Kevin16437/wheel_legged_robot/solidworks/轮腿装配图/守护兽轮腿.SLDASM

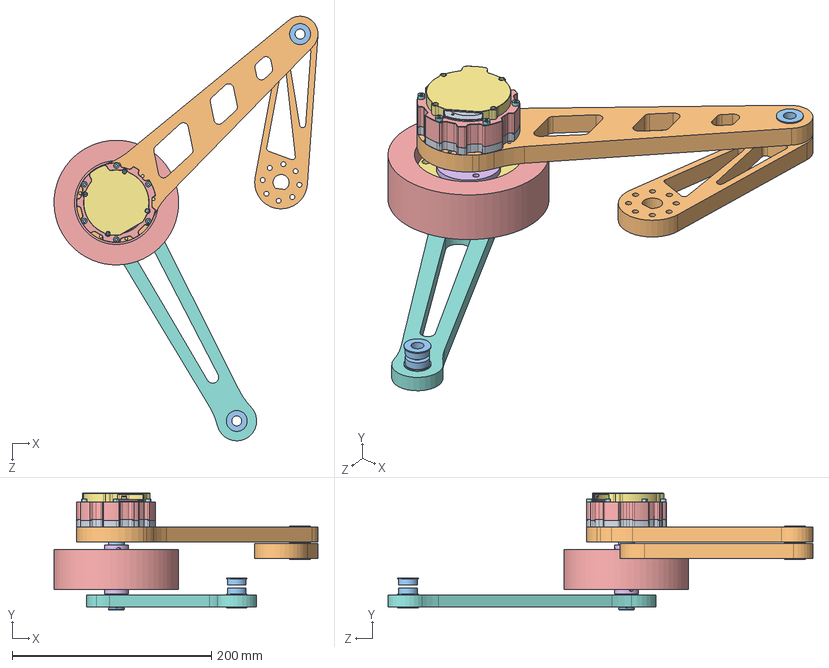
[picture p17: CAD file, 2024-12-23]
solidworks/轮腿装配图/守护兽轮腿.SLDASM
264.7 x 117.1 x 425.9 mm
NONE_1_1^_X2_897F683C00B79A6C51CF901F753_ASM_SG6010D_asm20240708.stp.STEP
SG6010H_ASM_______2__SG6-206444^_X2_897F683C00B79A6C51CF901F753_ASM_SG6010D_asm20240708.stp.STEP
MANIFOLD_SOLID_BREP_439152_1^SG6010C-04_5_ASM_1_ASM_SG6010C_ASM_252_ASM_1_ASM_SG6010D_asm20240708.stp.STEP
MANIFOLD_SOLID_BREP_439299_1^SG6010C-04_5_ASM_1_ASM_SG6010C_ASM_252_ASM_1_ASM_SG6010D_asm20240708.stp.STEP
SG6010C-01_63_1^SG6010C_ASM_252_ASM_1_ASM_SG6010D_asm20240708.stp.STEP
SG6010C-21_6_1^SG6010C_ASM_252_ASM_1_ASM_SG6010D_asm20240708.stp.STEP
SG6010C-02_27_1^SG6010C_ASM_252_ASM_1_ASM_SG6010D_asm20240708.stp.STEP
M3X22_2_1^SG6010C_ASM_252_ASM_1_ASM_SG6010D_asm20240708.stp.STEP x 6
M2X5_2_1^SG6010C_ASM_252_ASM_1_ASM_SG6010D_asm20240708.stp.STEP x 4
小腿臂
传动轴
内30外47高9轴承
轮
法兰内16外22 x 2
轮子固定板 x 2
小腿臂外侧
内16外40高12轴承
大腿臂
内10外19厚7法兰21厚1 x 6
内10外18推力球 x 2
传动轴垫片
4mm轴间垫片
1mm轴间垫片
