Kevin16437/wheel_legged_robot/solidworks/轮腿装配图/西格·马总装模型2024(二级减速).SLDASM

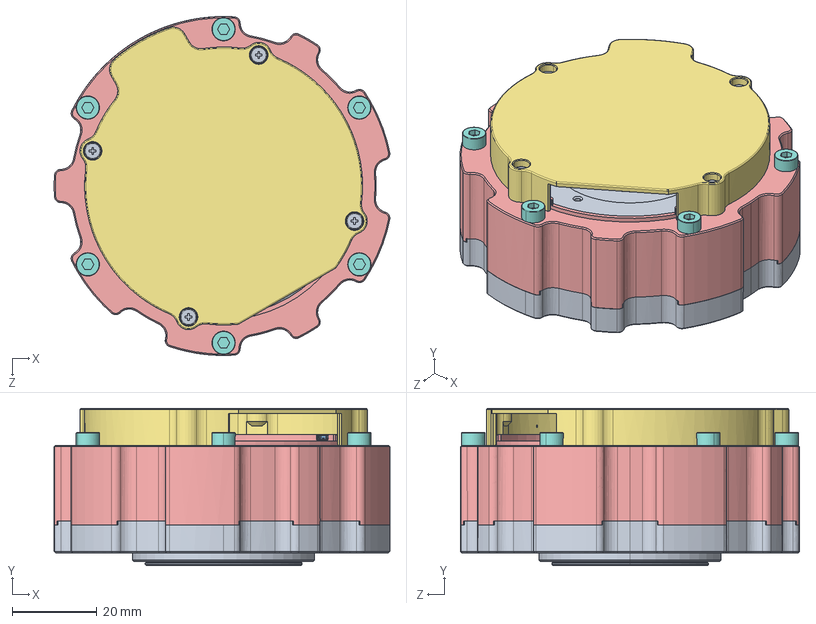
[picture p18: CAD file, 2024-12-23]
solidworks/轮腿装配图/西格·马总装模型2024(二级减速).SLDASM
79.2 x 37.1 x 80.0 mm
NONE_1_1^_X2_897F683C00B79A6C51CF901F753_ASM_SG6010D_asm20240708.stp.STEP
SG6010H_ASM_______2__SG6-206444^_X2_897F683C00B79A6C51CF901F753_ASM_SG6010D_asm20240708.stp.STEP
MANIFOLD_SOLID_BREP_439152_1^SG6010C-04_5_ASM_1_ASM_SG6010C_ASM_252_ASM_1_ASM_SG6010D_asm20240708.stp.STEP
MANIFOLD_SOLID_BREP_439299_1^SG6010C-04_5_ASM_1_ASM_SG6010C_ASM_252_ASM_1_ASM_SG6010D_asm20240708.stp.STEP
SG6010C-01_63_1^SG6010C_ASM_252_ASM_1_ASM_SG6010D_asm20240708.stp.STEP
SG6010C-21_6_1^SG6010C_ASM_252_ASM_1_ASM_SG6010D_asm20240708.stp.STEP
SG6010C-02_27_1^SG6010C_ASM_252_ASM_1_ASM_SG6010D_asm20240708.stp.STEP
M3X22_2_1^SG6010C_ASM_252_ASM_1_ASM_SG6010D_asm20240708.stp.STEP x 6
M2X5_2_1^SG6010C_ASM_252_ASM_1_ASM_SG6010D_asm20240708.stp.STEP x 4
