Kevin16437/wheel_legged_robot/solidworks/轮腿零件step/轮子固定板x4.STEP

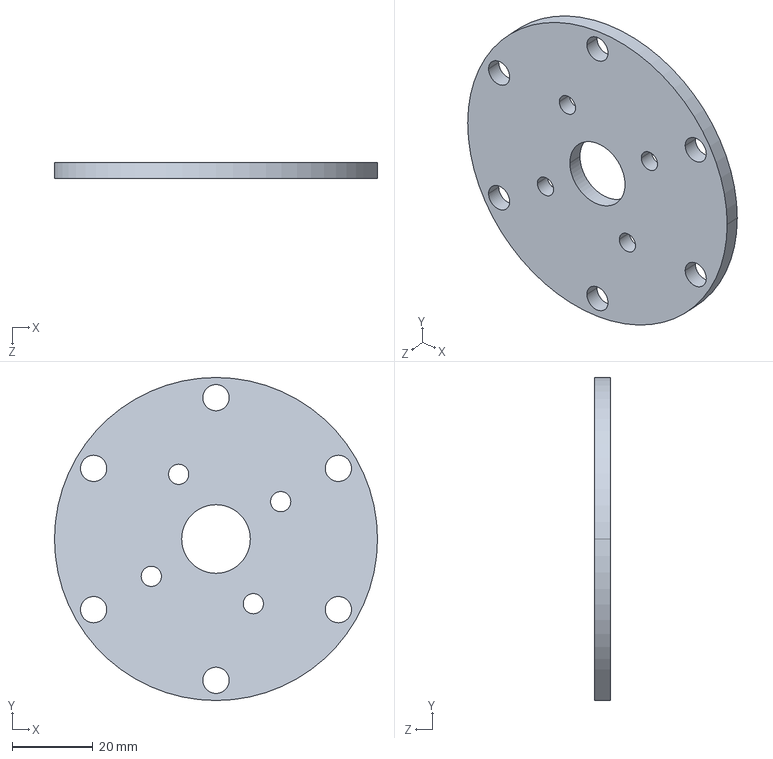
[picture p20: CAD file, 2024-12-23]
solidworks/轮腿零件step/轮子固定板x4.STEP
80.0 x 80.0 x 4.00 mm
