Kevin16437/wheel_legged_robot/solidworks/轮腿零件step/底部电池斜壳x1-碳板.STEP

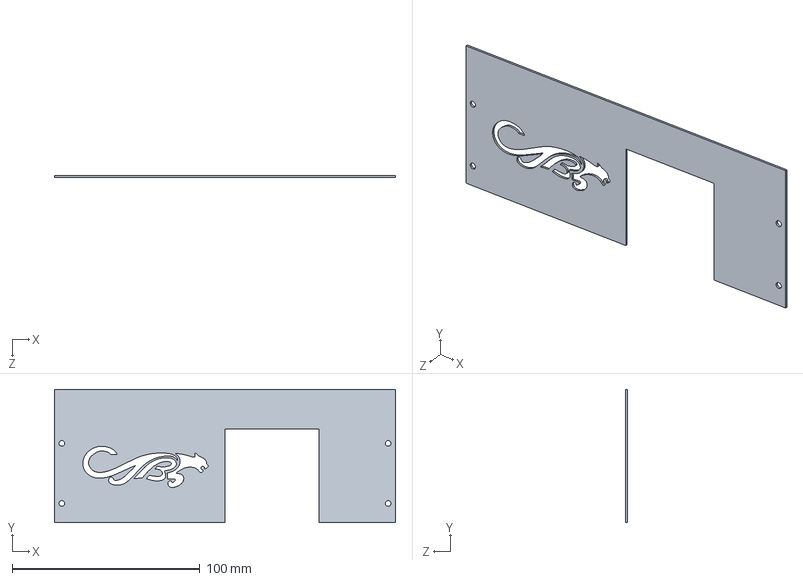
[picture p21: CAD file, 2024-12-23]
solidworks/轮腿零件step/底部电池斜壳x1-碳板.STEP
181.7 x 71.0 x 1.00 mm
