Kevin16437/wheel_legged_robot/solidworks/轮腿零件step/守护兽强挡板x1-碳板.STEP

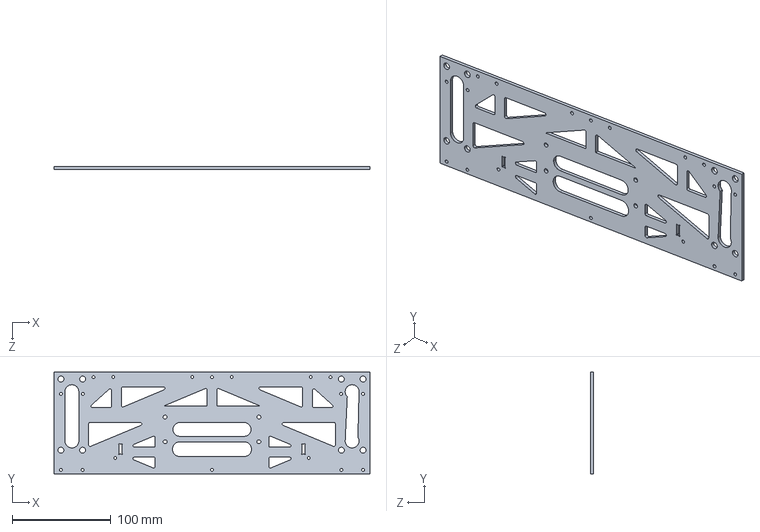
[picture p22: CAD file, 2024-12-23]
solidworks/轮腿零件step/守护兽强挡板x1-碳板.STEP
320.0 x 103.0 x 3.00 mm
