Kevin16437/wheel_legged_robot/solidworks/轮腿零件step/关节电机固定盒x1-碳板.STEP

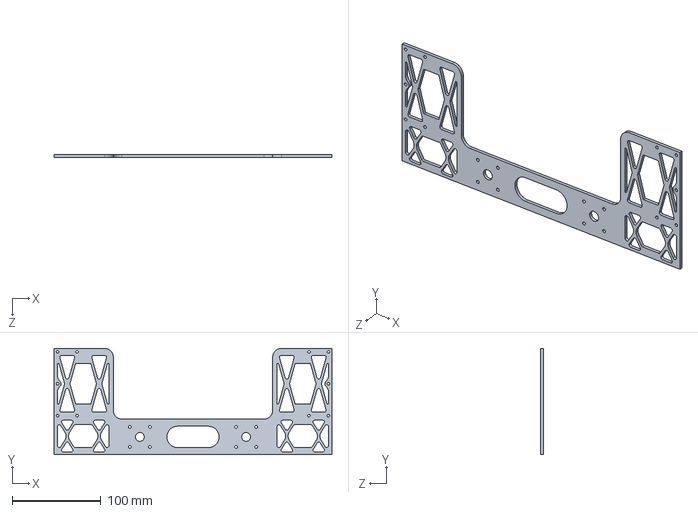
[picture p23: CAD file, 2024-12-23]
solidworks/轮腿零件step/关节电机固定盒x1-碳板.STEP
314.0 x 120.0 x 3.00 mm
