Kevin16437/wheel_legged_robot/solidworks/轮腿零件step/KJ90FT33装配体x2.STEP

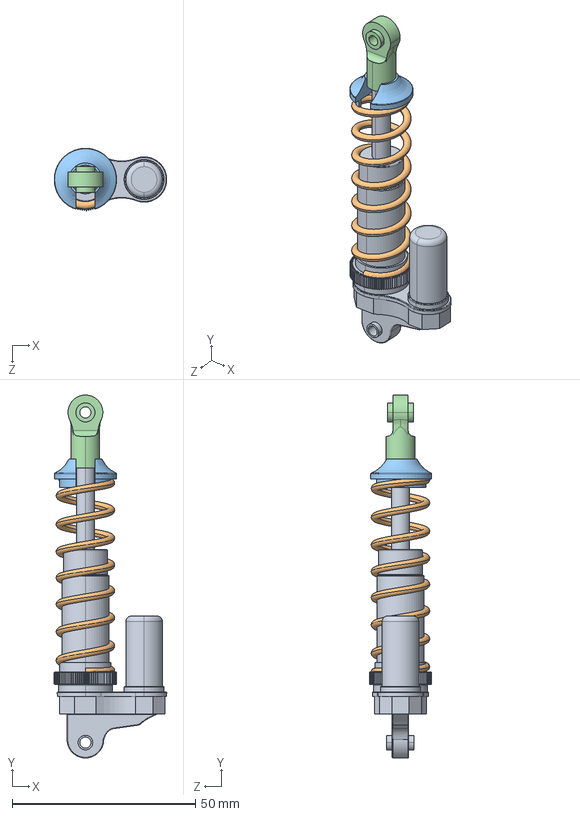
[picture p24: CAD file, 2024-12-23]
solidworks/轮腿零件step/KJ90FT33装配体x2.STEP
30.7 x 99.0 x 17.0 mm
________.STEP
____90____.STEP
________-0.STEP
________-1.STEP
