Kevin16437/wheel_legged_robot/solidworks/轮腿零件step/内10外30厚11导轮x4.STEP

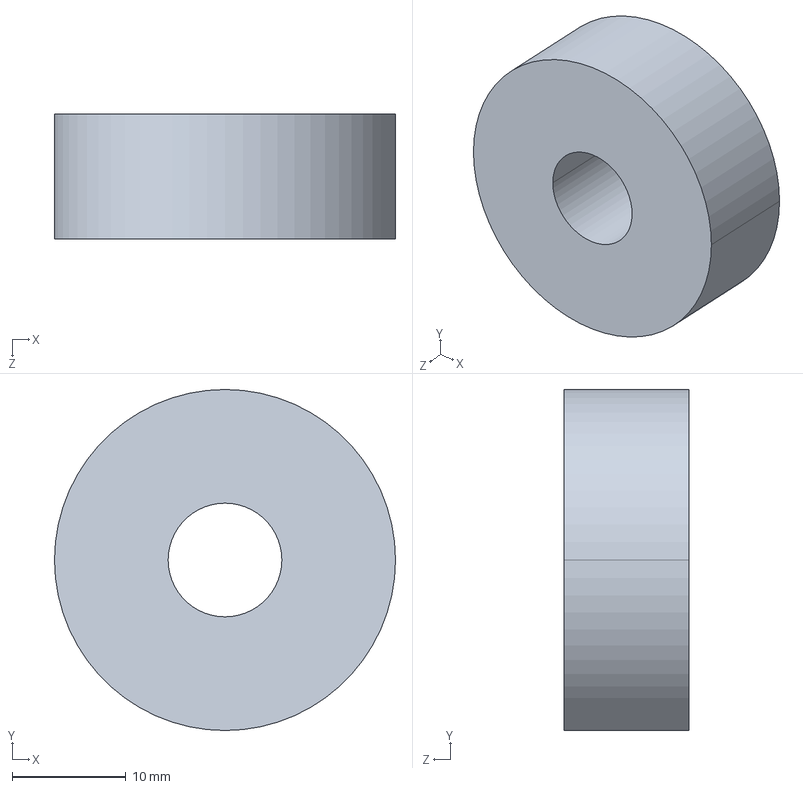
[picture p25: CAD file, 2024-12-23]
solidworks/轮腿零件step/内10外30厚11导轮x4.STEP
30.0 x 30.0 x 11.0 mm
