Kevin16437/wheel_legged_robot/solidworks/轮腿零件step/守护兽强挡板短x1-碳板.STEP

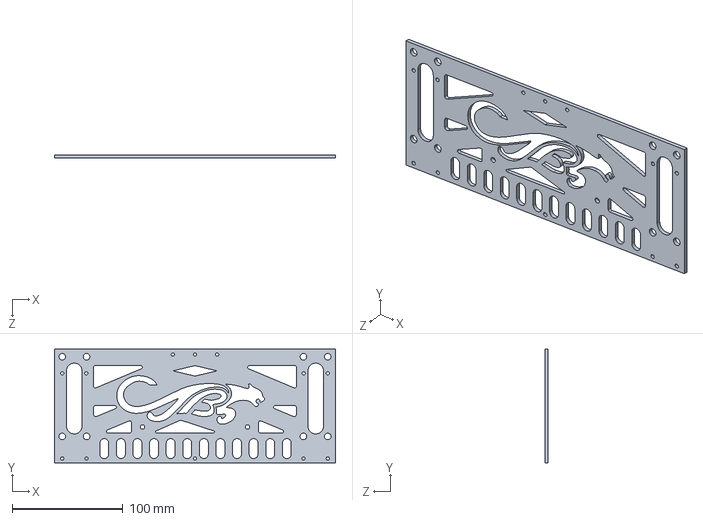
[picture p27: CAD file, 2024-12-23]
solidworks/轮腿零件step/守护兽强挡板短x1-碳板.STEP
254.0 x 103.0 x 3.00 mm
