Kevin16437/wheel_legged_robot/solidworks/轮腿零件step/内16外40高12轴承x4.STEP

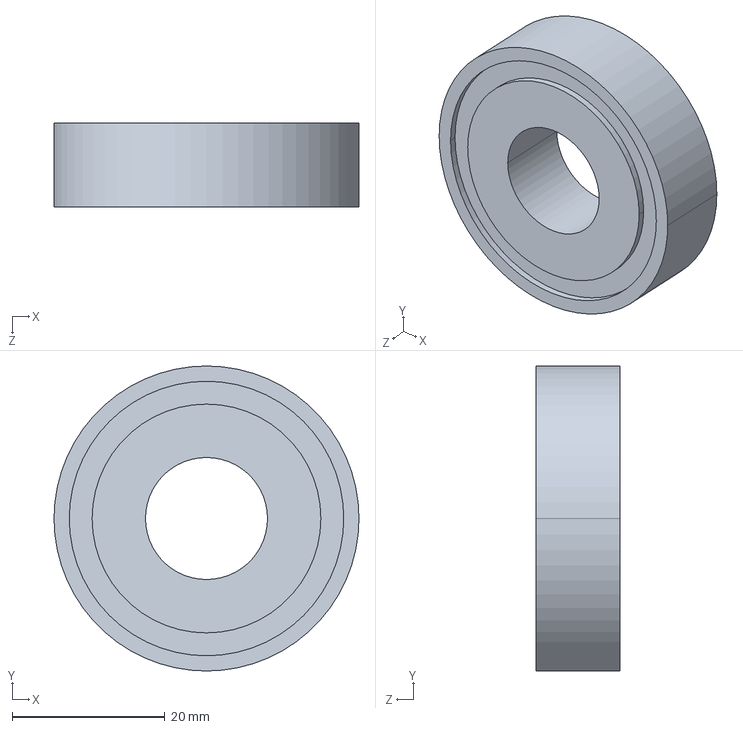
[picture p28: CAD file, 2024-12-23]
solidworks/轮腿零件step/内16外40高12轴承x4.STEP
40.0 x 40.0 x 11.0 mm
