Kevin16437/wheel_legged_robot/solidworks/轮腿零件step/云台底板方避震x1.STEP

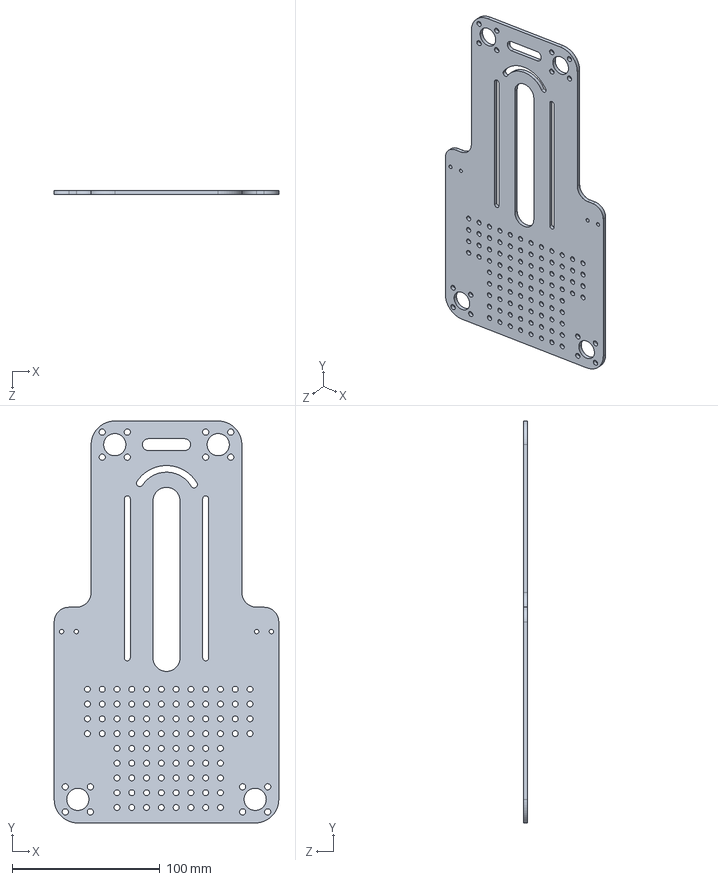
[picture p29: CAD file, 2024-12-23]
solidworks/轮腿零件step/云台底板方避震x1.STEP
152.0 x 272.0 x 3.00 mm
