Kevin16437/wheel_legged_robot/solidworks/轮腿零件step/关节电机固定盒上下x2-碳板.STEP

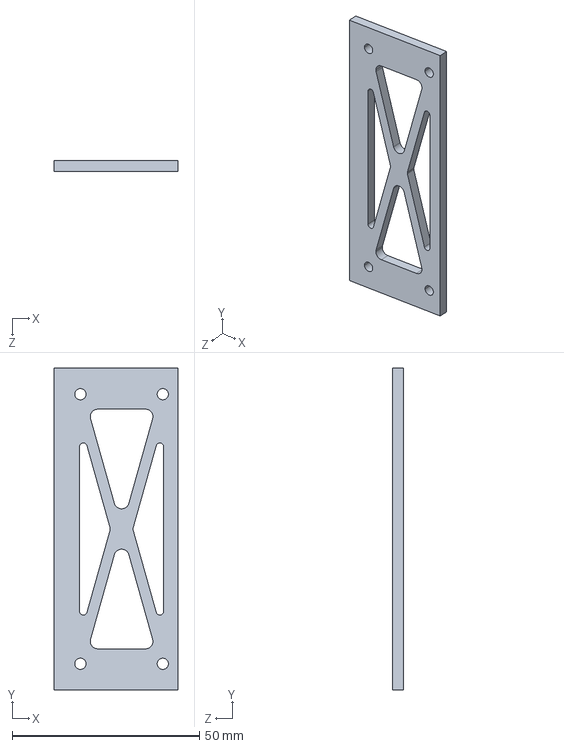
[picture p30: CAD file, 2024-12-23]
solidworks/轮腿零件step/关节电机固定盒上下x2-碳板.STEP
33.0 x 86.0 x 3.00 mm
