Kevin16437/wheel_legged_robot/solidworks/轮腿零件step/电源.STEP

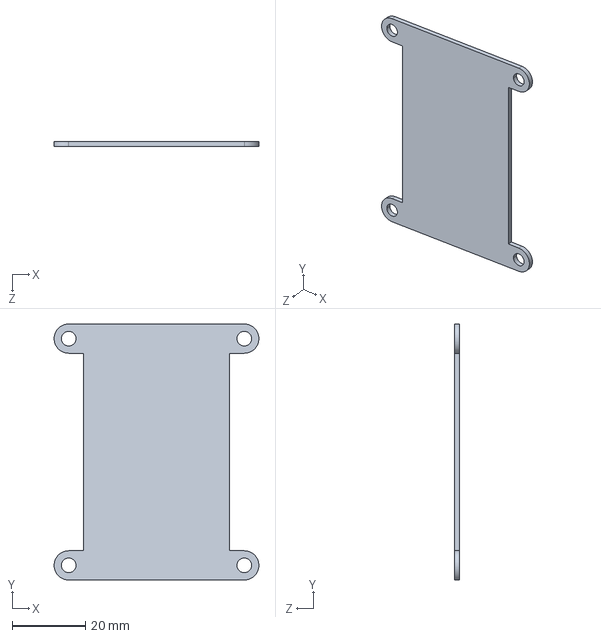
[picture p31: CAD file, 2024-12-23]
solidworks/轮腿零件step/电源.STEP
56.0 x 70.0 x 1.50 mm
