Kevin16437/wheel_legged_robot/solidworks/轮腿零件step/塞打螺栓D10XM8-16x4.STEP

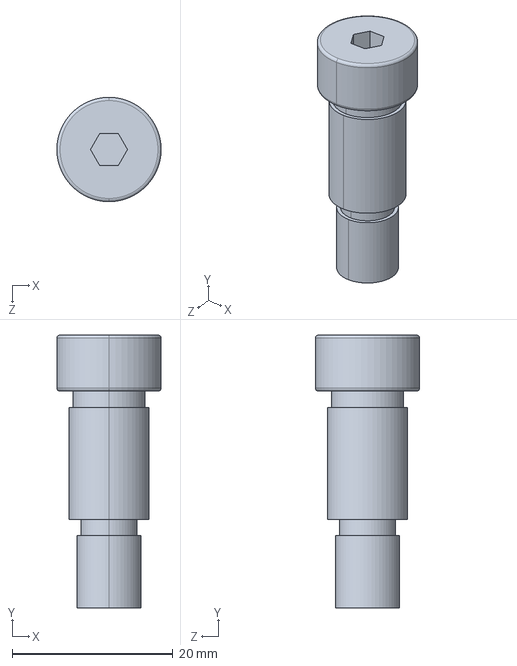
[picture p32: CAD file, 2024-12-23]
solidworks/轮腿零件step/塞打螺栓D10XM8-16x4.STEP
13.0 x 34.0 x 13.0 mm
