Kevin16437/wheel_legged_robot/solidworks/轮腿零件step/四方体固定x44.STEP

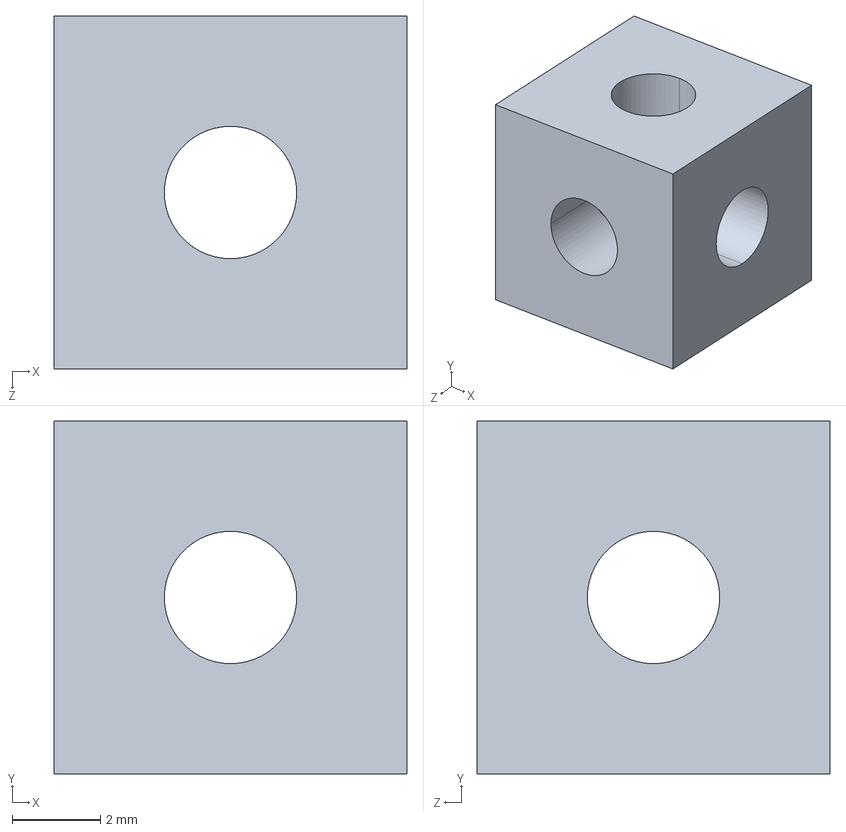
[picture p33: CAD file, 2024-12-23]
solidworks/轮腿零件step/四方体固定x44.STEP
8.00 x 8.00 x 8.00 mm
