Kevin16437/wheel_legged_robot/solidworks/轮腿零件step/限位挡块x2.STEP

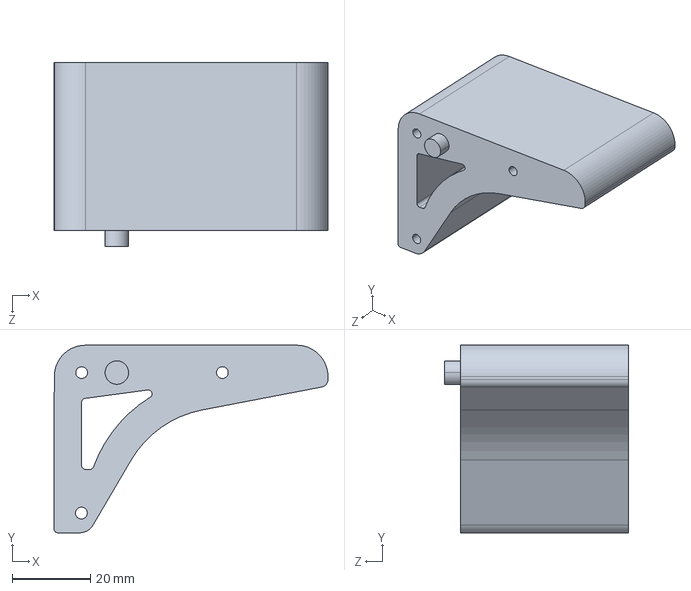
[picture p34: CAD file, 2024-12-23]
solidworks/轮腿零件step/限位挡块x2.STEP
70.1 x 48.0 x 47.0 mm
