Kevin16437/wheel_legged_robot/solidworks/轮腿零件step/轴承挡板x4-碳板.STEP

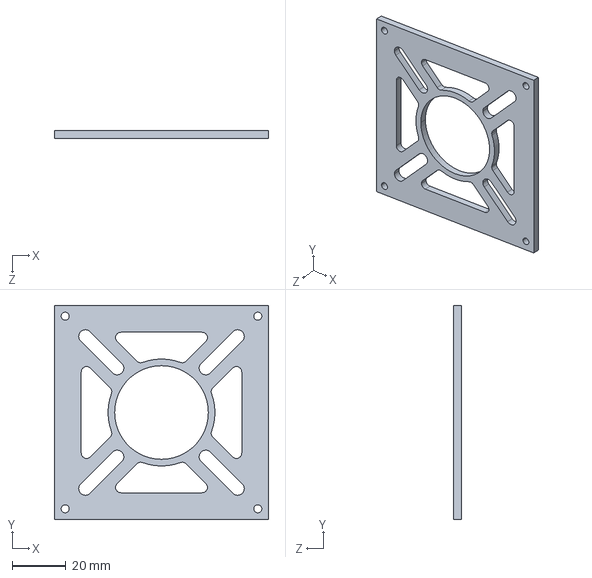
[picture p35: CAD file, 2024-12-23]
solidworks/轮腿零件step/轴承挡板x4-碳板.STEP
80.0 x 80.0 x 3.00 mm
