Kevin16437/wheel_legged_robot/solidworks/轮腿零件step/轴承支撑板整体x2-碳板.STEP

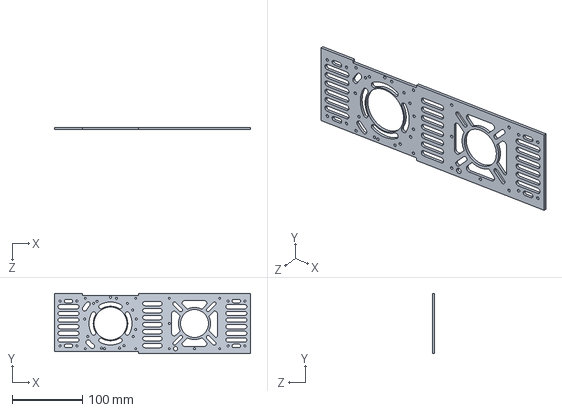
[picture p37: CAD file, 2024-12-23]
solidworks/轮腿零件step/轴承支撑板整体x2-碳板.STEP
280.0 x 86.0 x 3.00 mm
