Kevin16437/wheel_legged_robot/solidworks/轮腿零件step/下底盘保护x2-碳板.STEP

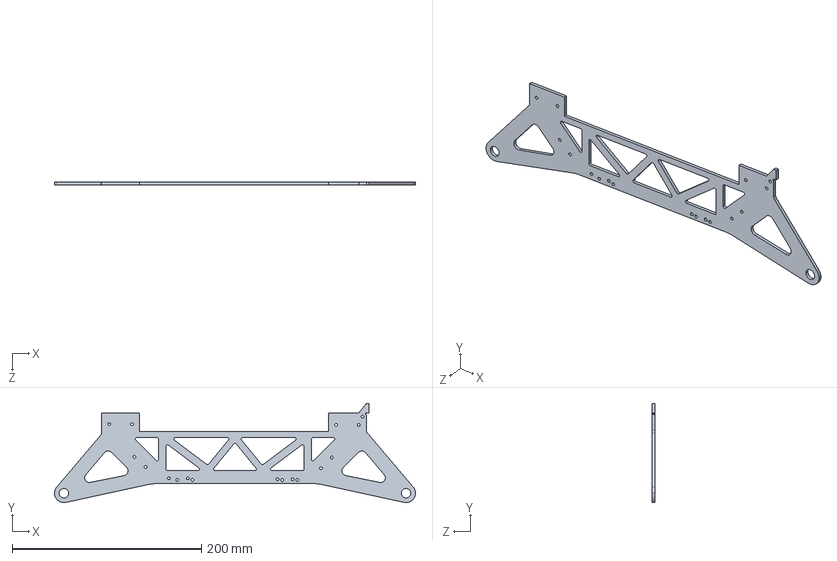
[picture p39: CAD file, 2024-12-23]
solidworks/轮腿零件step/下底盘保护x2-碳板.STEP
382.0 x 105.0 x 3.00 mm
