Kevin16437/wheel_legged_robot/solidworks/轮腿装配图/传动轴.SLDPRT

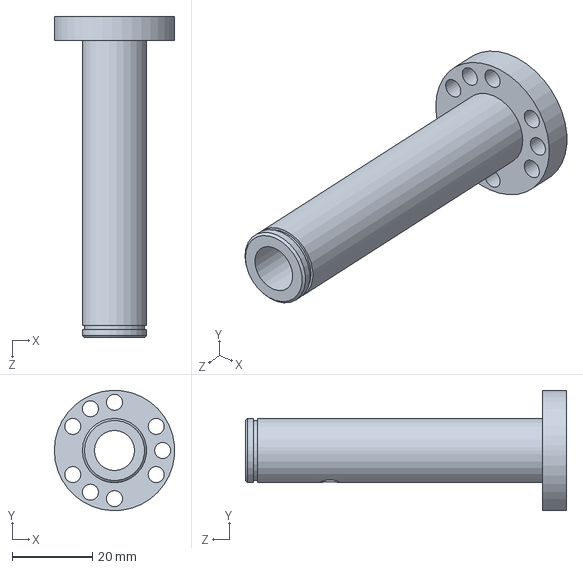
[picture p40: CAD file, 2024-12-23]
solidworks/轮腿装配图/传动轴.SLDPRT
30.0 x 30.0 x 80.0 mm
