Kevin16437/wheel_legged_robot/solidworks/轮腿零件step/长方体固定x8.STEP

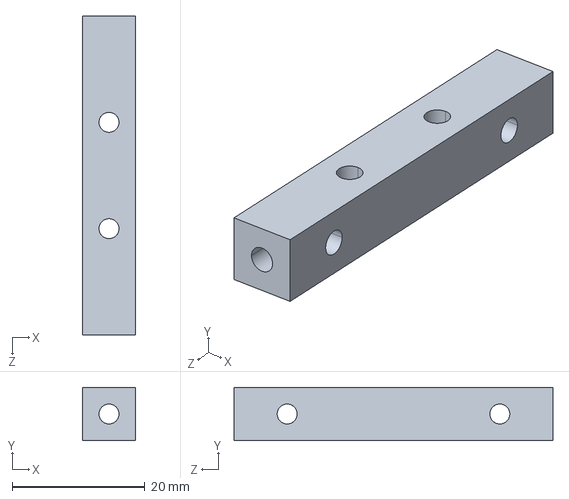
[picture p41: CAD file, 2024-12-23]
solidworks/轮腿零件step/长方体固定x8.STEP
8.00 x 8.00 x 48.0 mm
