Kevin16437/wheel_legged_robot/solidworks/轮腿装配图/大腿臂.SLDPRT

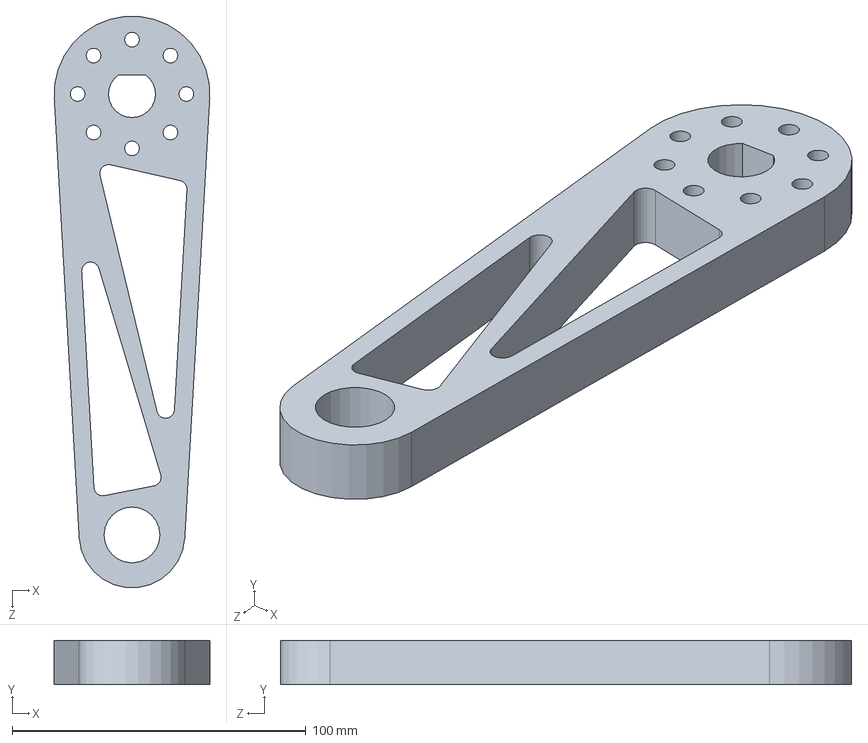
[picture p42: CAD file, 2024-12-23]
solidworks/轮腿装配图/大腿臂.SLDPRT
52.9 x 15.0 x 194.3 mm
