Kevin16437/wheel_legged_robot/solidworks/轮腿零件step/3mm避震安装座x2.STEP

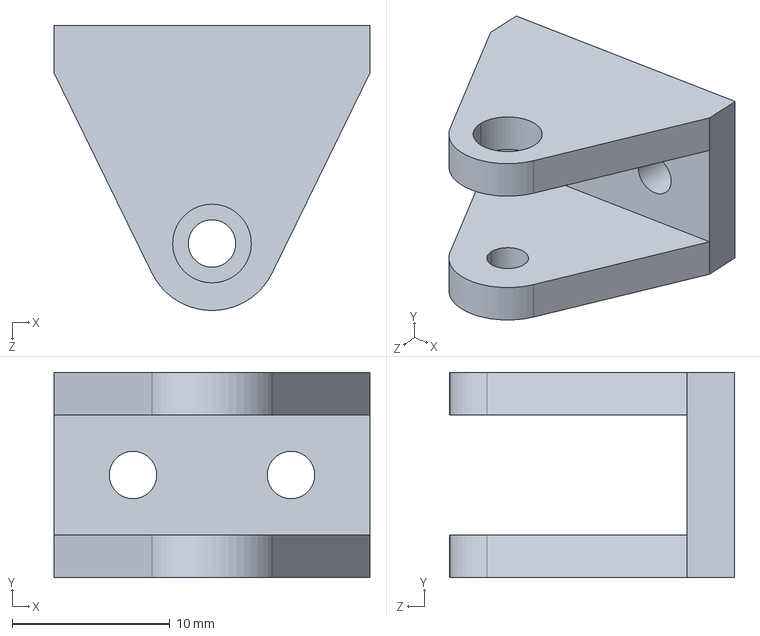
[picture p43: CAD file, 2024-12-23]
solidworks/轮腿零件step/3mm避震安装座x2.STEP
20.0 x 13.0 x 18.0 mm
