Kevin16437/wheel_legged_robot/solidworks/轮腿零件step/传动轴关节电机长x2.STEP

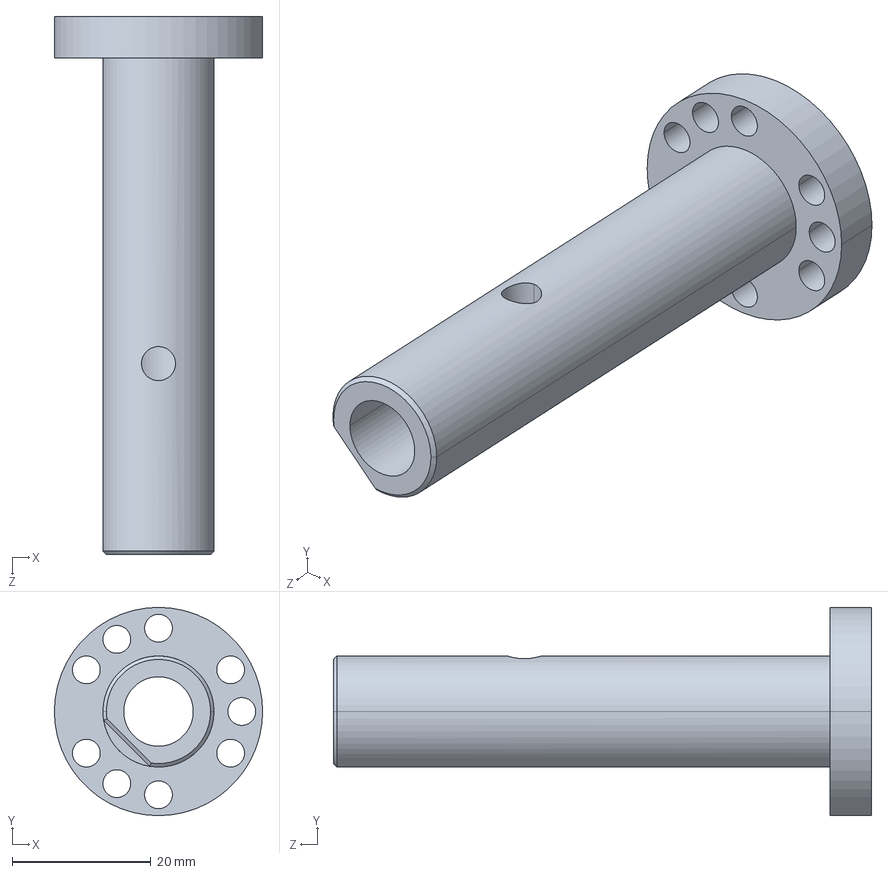
[picture p44: CAD file, 2024-12-23]
solidworks/轮腿零件step/传动轴关节电机长x2.STEP
30.0 x 30.0 x 77.5 mm
