Kevin16437/wheel_legged_robot/solidworks/轮腿零件step/底盘底面壳x1-碳板.STEP

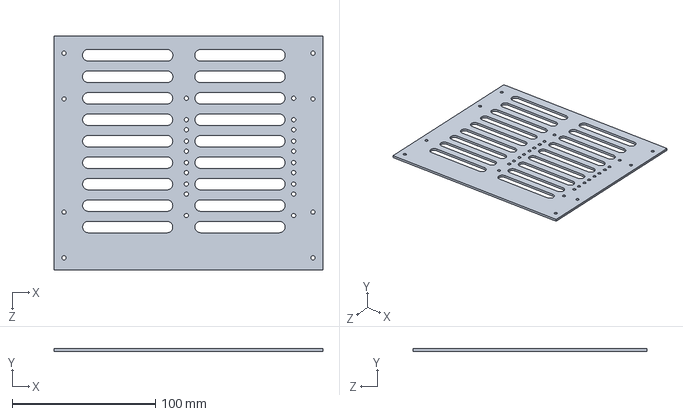
[picture p45: CAD file, 2024-12-23]
solidworks/轮腿零件step/底盘底面壳x1-碳板.STEP
188.0 x 2.00 x 163.5 mm
