Kevin16437/wheel_legged_robot/solidworks/轮腿零件step/光轴固定座内8x8.STEP

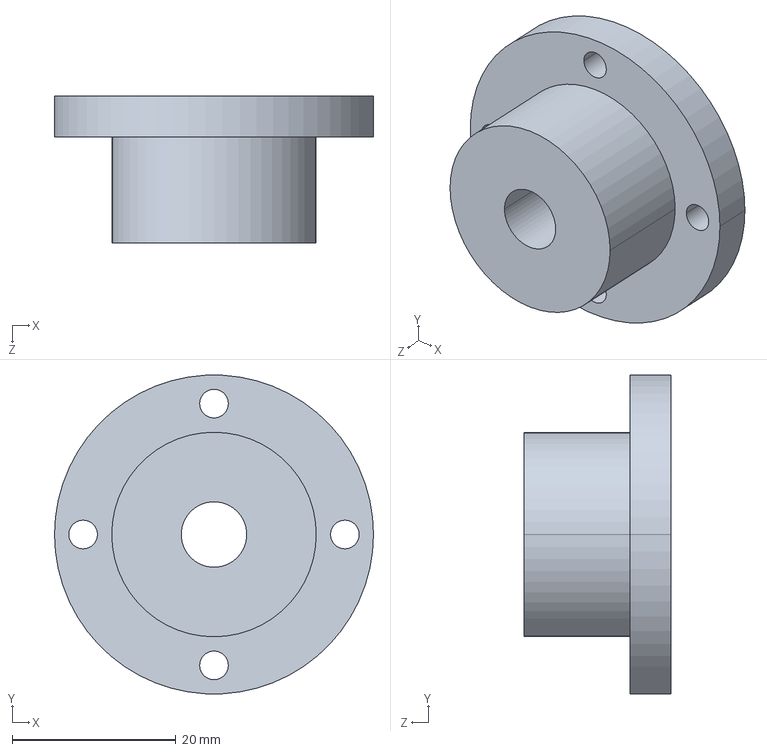
[picture p46: CAD file, 2024-12-23]
solidworks/轮腿零件step/光轴固定座内8x8.STEP
39.0 x 38.9 x 18.0 mm
