Kevin16437/wheel_legged_robot/solidworks/轮腿装配图/4mm轴间垫片.SLDPRT

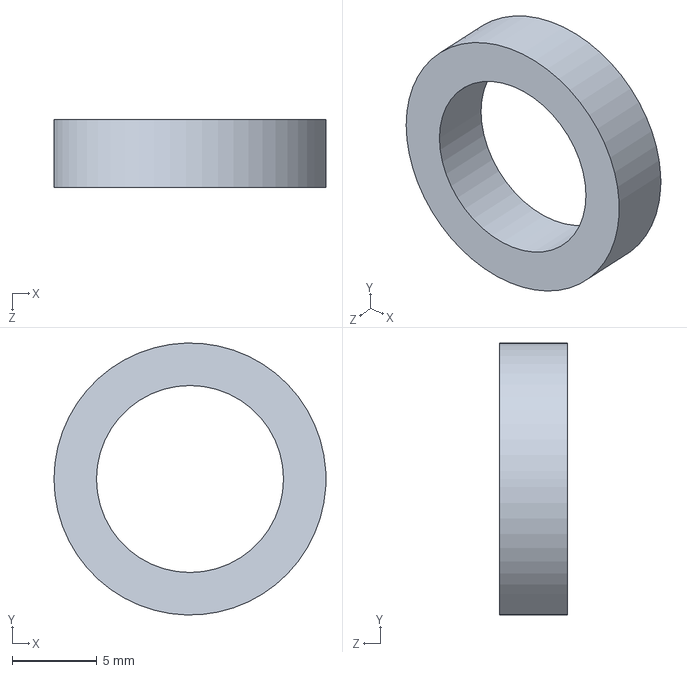
[picture p48: CAD file, 2024-12-23]
solidworks/轮腿装配图/4mm轴间垫片.SLDPRT
16.0 x 16.0 x 4.00 mm
