Kevin16437/wheel_legged_robot/solidworks/轮腿零件step/小腿臂外侧x2.STEP

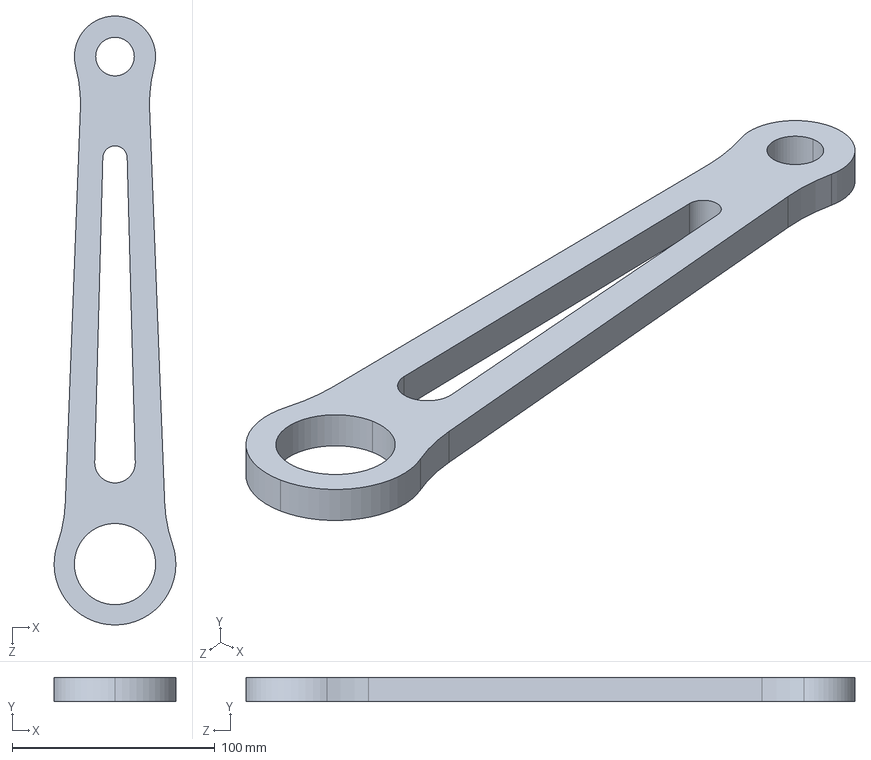
[picture p49: CAD file, 2024-12-23]
solidworks/轮腿零件step/小腿臂外侧x2.STEP
60.0 x 12.0 x 300.0 mm
