Kevin16437/wheel_legged_robot/solidworks/轮腿零件step/底盘加强横梁守护兽长.STEP

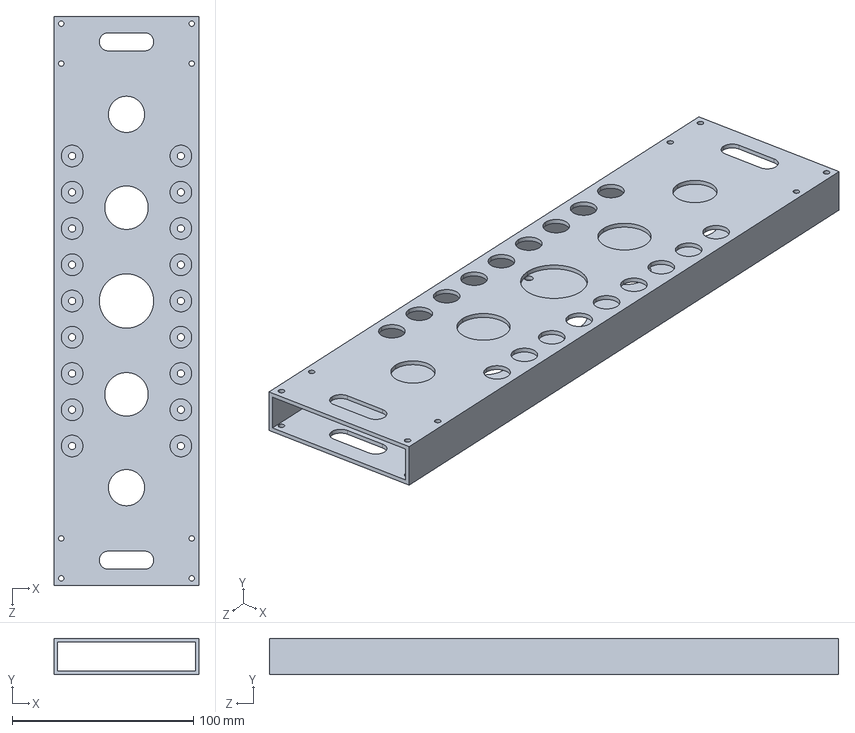
[picture p50: CAD file, 2024-12-23]
solidworks/轮腿零件step/底盘加强横梁守护兽长.STEP
80.0 x 20.0 x 314.0 mm
