Kevin16437/wheel_legged_robot/solidworks/轮腿零件step/100mm光轴x4.STEP

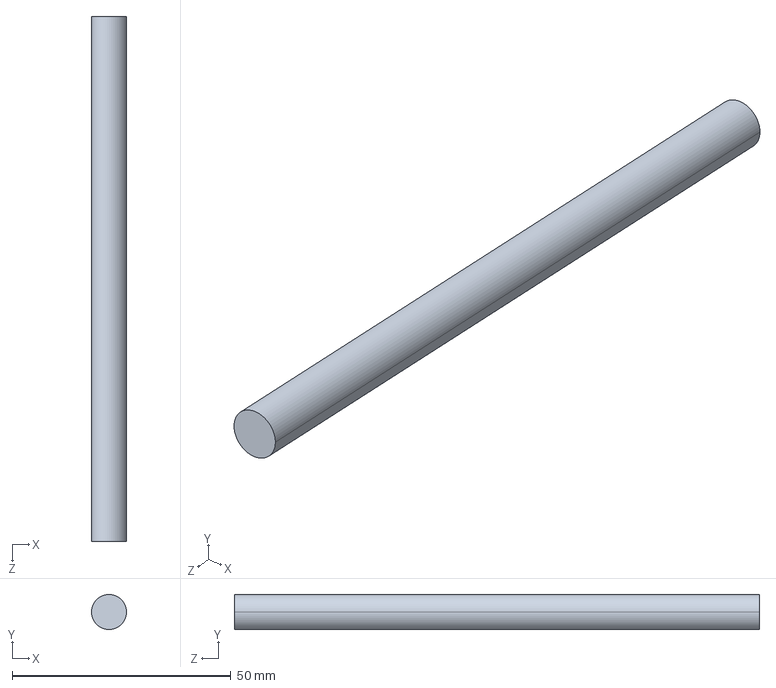
[picture p51: CAD file, 2024-12-23]
solidworks/轮腿零件step/100mm光轴x4.STEP
8.00 x 8.00 x 120.0 mm
