Kevin16437/wheel_legged_robot/solidworks/轮腿零件step/内10外19厚7法兰21厚1x10.STEP

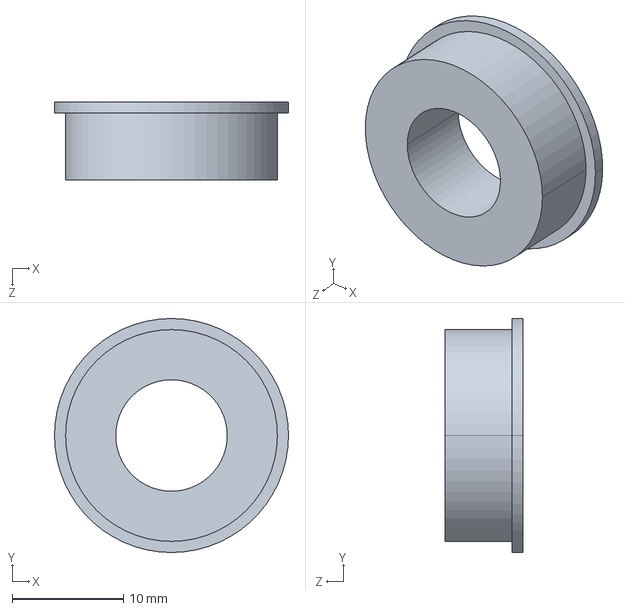
[picture p52: CAD file, 2024-12-23]
solidworks/轮腿零件step/内10外19厚7法兰21厚1x10.STEP
21.0 x 21.0 x 7.00 mm
