Kevin16437/wheel_legged_robot/solidworks/轮腿零件step/底盘定位x1-碳板.STEP

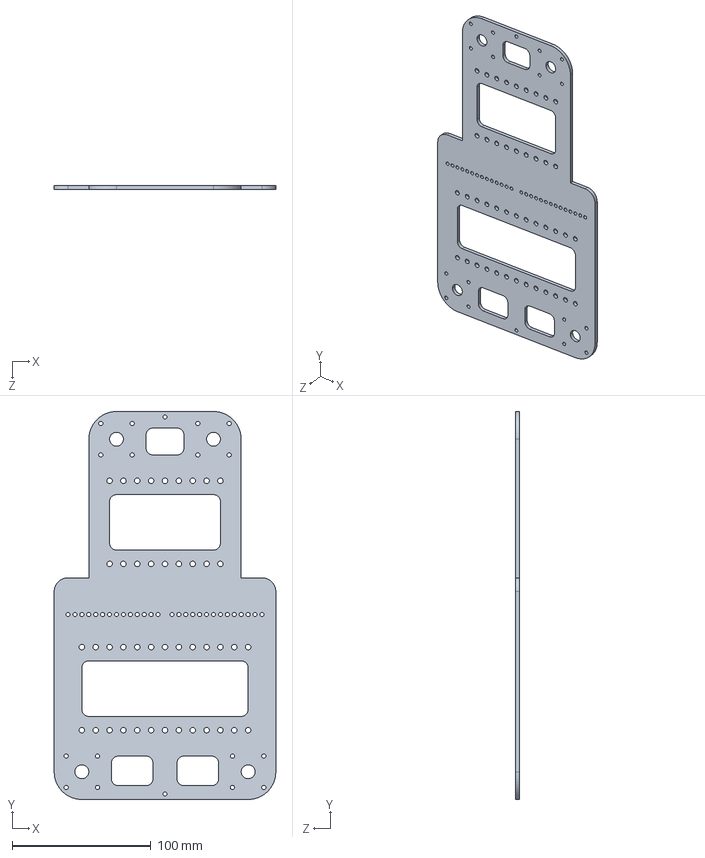
[picture p53: CAD file, 2024-12-23]
solidworks/轮腿零件step/底盘定位x1-碳板.STEP
160.0 x 280.0 x 3.00 mm
