Kevin16437/wheel_legged_robot/solidworks/轮腿零件step/法兰内16外22.STEP

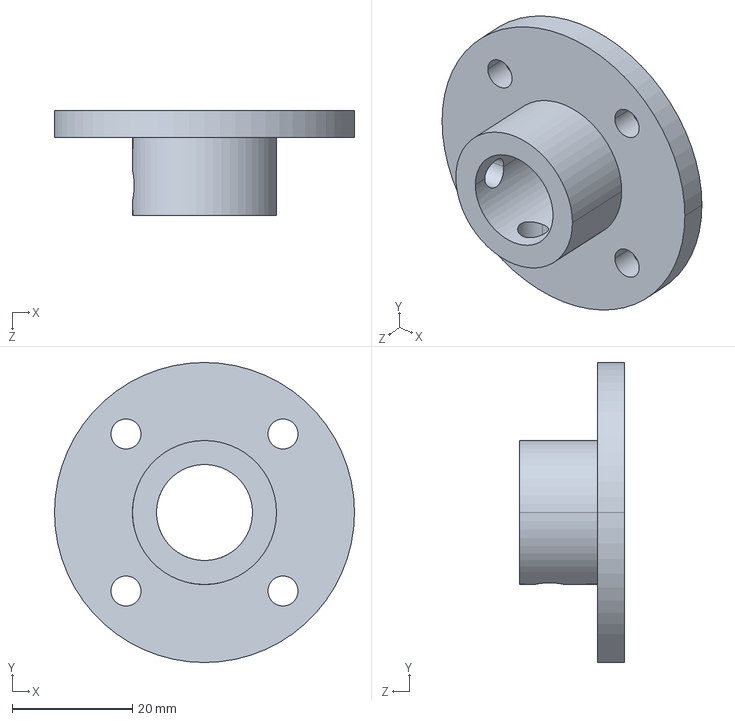
[picture p55: CAD file, 2024-12-23]
solidworks/轮腿零件step/法兰内16外22.STEP
50.0 x 50.0 x 17.5 mm
