Kevin16437/wheel_legged_robot/solidworks/轮腿零件step/内10外18推力球x4.STEP

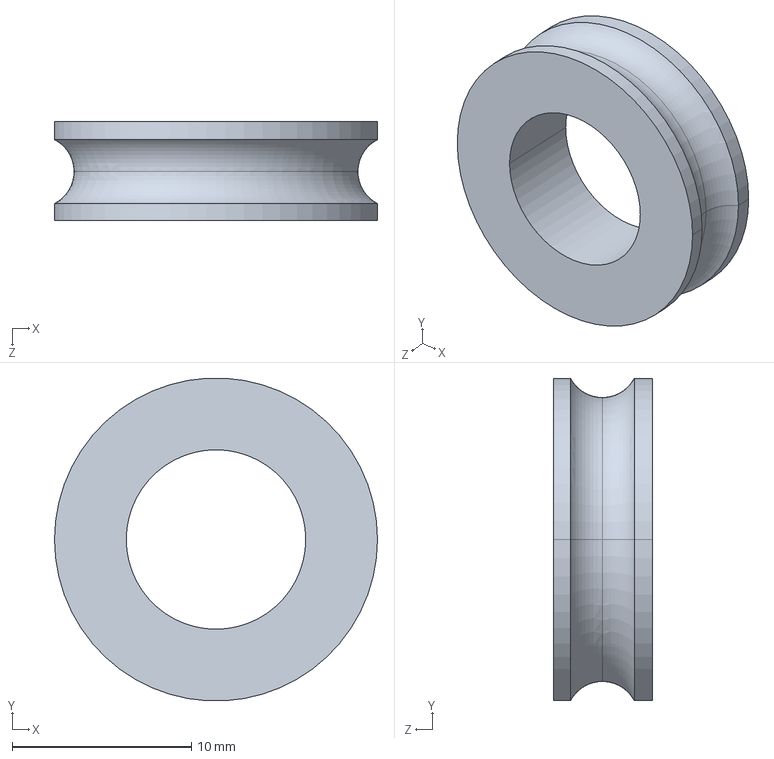
[picture p56: CAD file, 2024-12-23]
solidworks/轮腿零件step/内10外18推力球x4.STEP
18.0 x 18.0 x 5.50 mm
