Kevin16437/wheel_legged_robot/solidworks/轮腿零件step/传动轴垫片x2.STEP

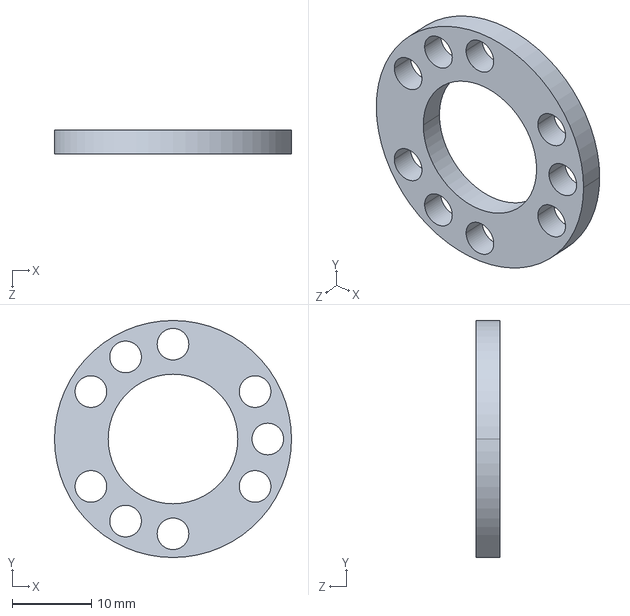
[picture p57: CAD file, 2024-12-23]
solidworks/轮腿零件step/传动轴垫片x2.STEP
30.0 x 30.0 x 3.00 mm
