Kevin16437/wheel_legged_robot/solidworks/轮腿零件step/轴承支撑板护板x2-碳板.STEP

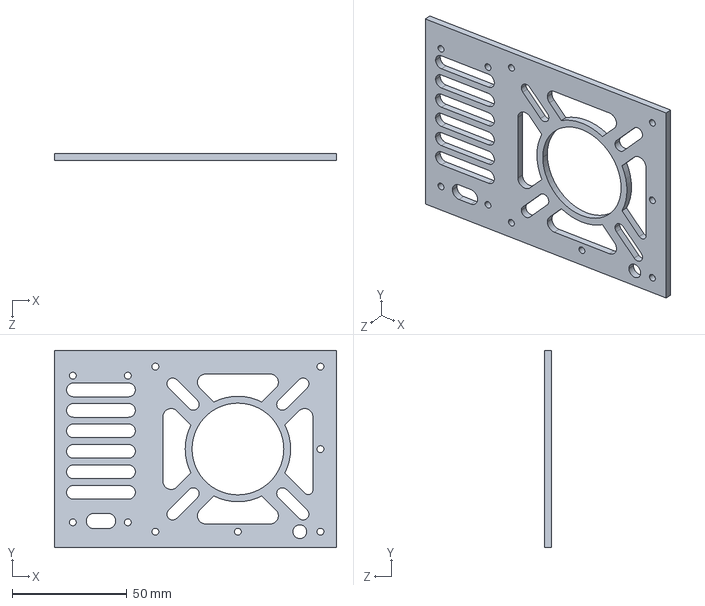
[picture p58: CAD file, 2024-12-23]
solidworks/轮腿零件step/轴承支撑板护板x2-碳板.STEP
123.0 x 86.0 x 3.00 mm
