Kevin16437/wheel_legged_robot/solidworks/轮腿零件step/整体电机固定盒x1-碳板.STEP

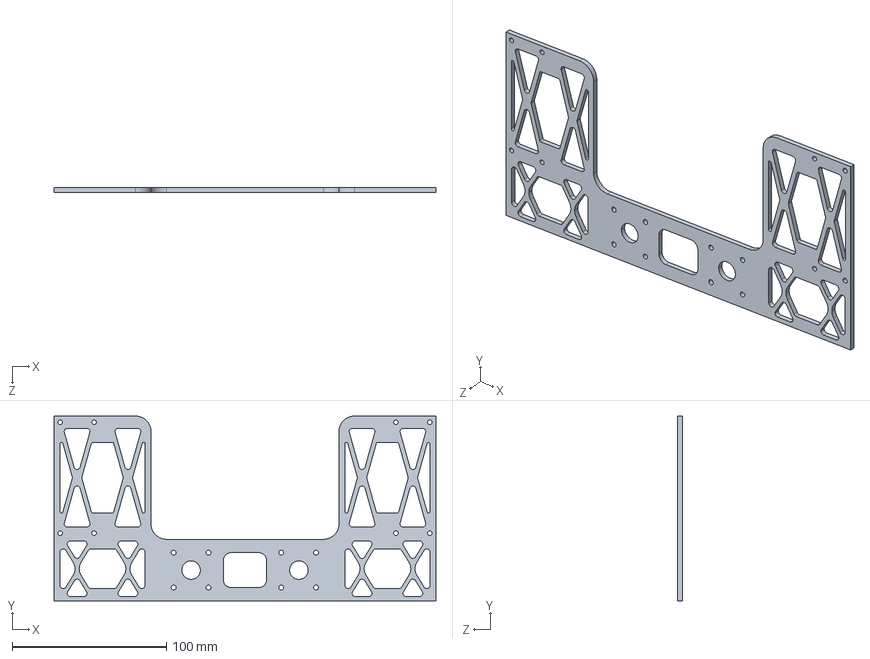
[picture p59: CAD file, 2024-12-23]
solidworks/轮腿零件step/整体电机固定盒x1-碳板.STEP
248.0 x 120.0 x 3.00 mm
