Kevin16437/wheel_legged_robot/solidworks/轮腿零件step/内30外47高9轴承x4.STEP

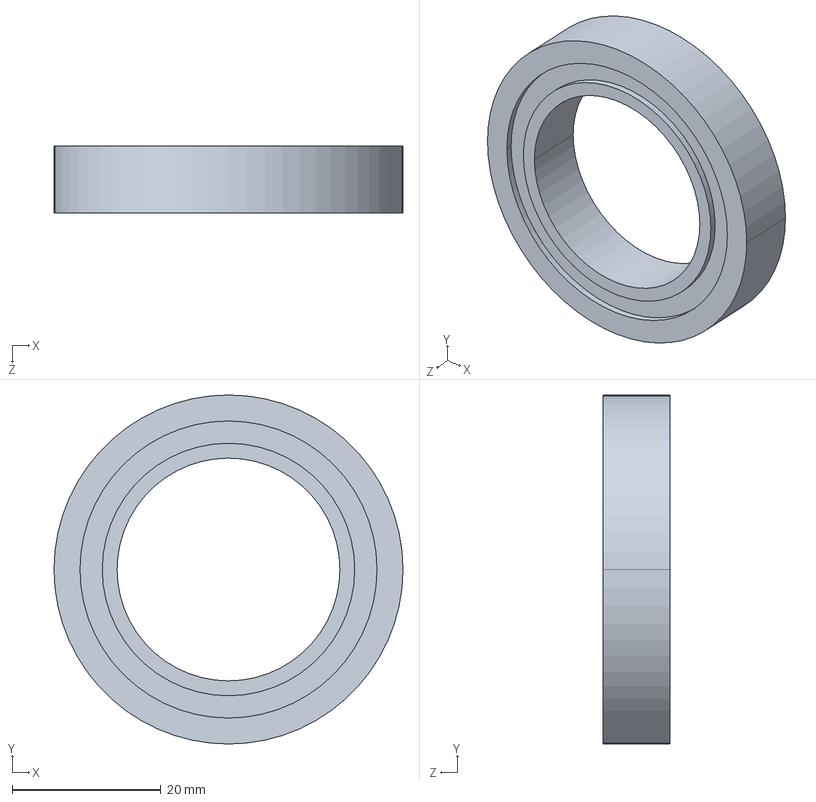
[picture p61: CAD file, 2024-12-23]
solidworks/轮腿零件step/内30外47高9轴承x4.STEP
47.0 x 47.0 x 9.00 mm
