Kevin16437/wheel_legged_robot/solidworks/轮腿零件step/3mm厚垫片x2.STEP

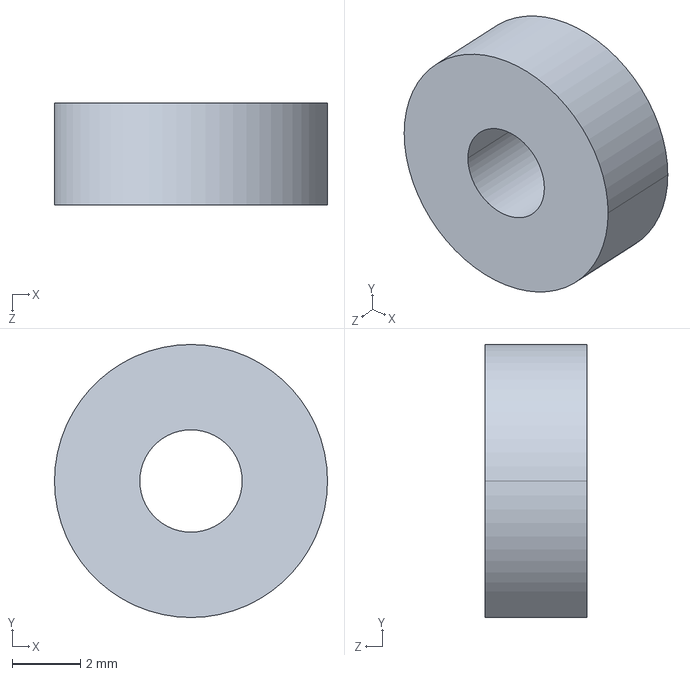
[picture p62: CAD file, 2024-12-23]
solidworks/轮腿零件step/3mm厚垫片x2.STEP
8.00 x 8.00 x 3.00 mm
