Kevin16437/wheel_legged_robot/solidworks/轮腿零件step/法兰直线轴承x4.STEP

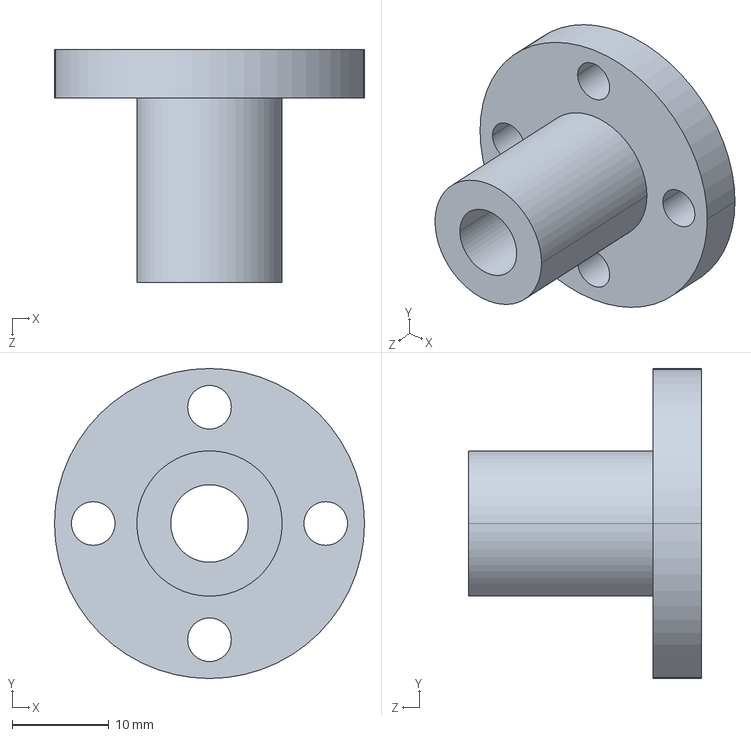
[picture p63: CAD file, 2024-12-23]
solidworks/轮腿零件step/法兰直线轴承x4.STEP
32.0 x 32.0 x 24.0 mm
