Kevin16437/wheel_legged_robot/solidworks/轮腿零件step/小腿臂x2-碳板.STEP

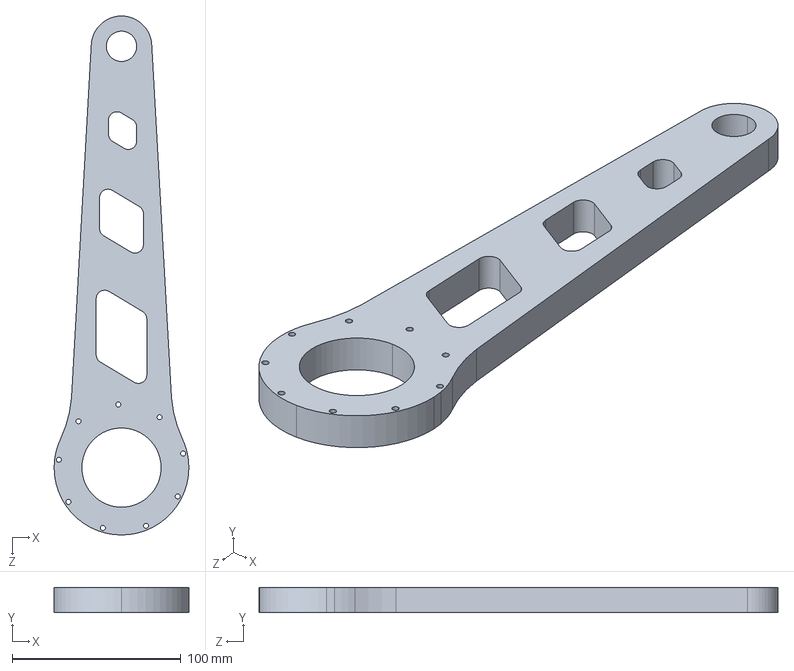
[picture p64: CAD file, 2024-12-23]
solidworks/轮腿零件step/小腿臂x2-碳板.STEP
80.0 x 15.0 x 308.0 mm
