Kevin16437/wheel_legged_robot/solidworks/轮腿零件step/底部前后斜壳x1-碳板.STEP

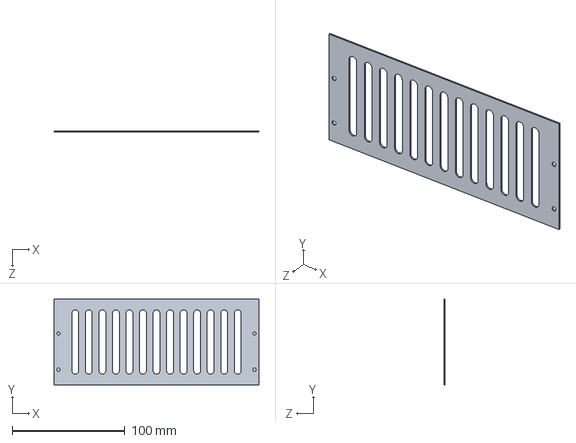
[picture p65: CAD file, 2024-12-23]
solidworks/轮腿零件step/底部前后斜壳x1-碳板.STEP
181.8 x 76.0 x 1.00 mm
