Kevin16437/wheel_legged_robot/solidworks/轮腿零件step/轮x2.STEP

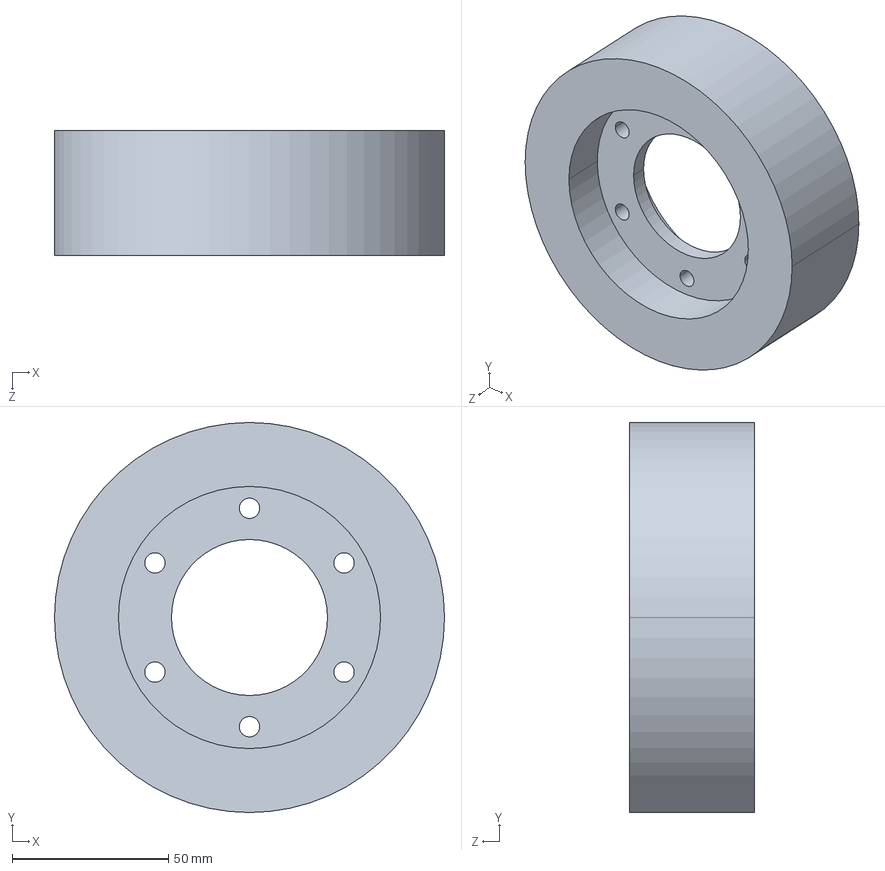
[picture p66: CAD file, 2024-12-23]
solidworks/轮腿零件step/轮x2.STEP
125.0 x 125.0 x 40.0 mm
