Kevin16437/wheel_legged_robot/solidworks/轮腿零件step/内14.7卡簧.STEP

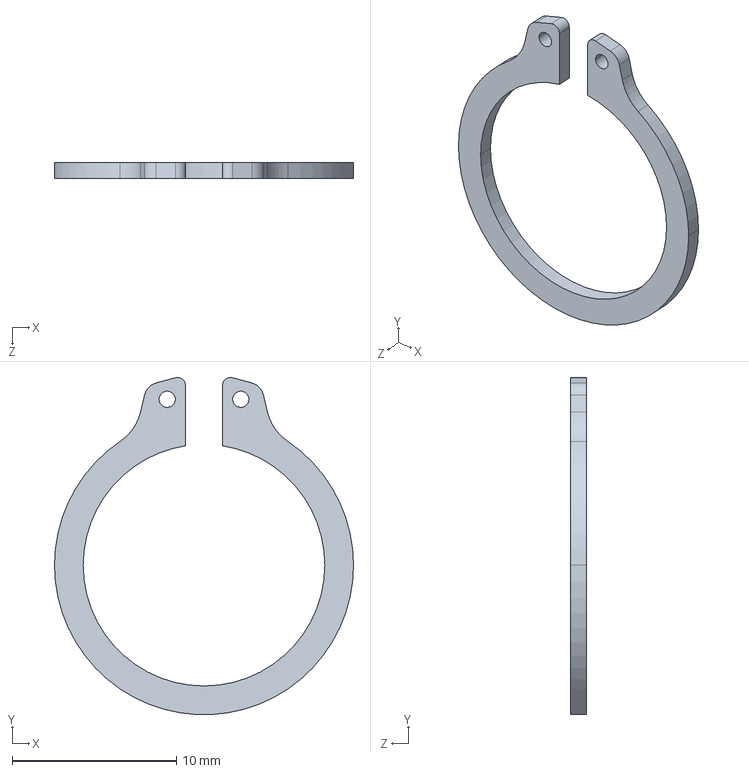
[picture p67: CAD file, 2024-12-23]
solidworks/轮腿零件step/内14.7卡簧.STEP
18.2 x 20.5 x 1.00 mm
