Kevin16437/wheel_legged_robot/solidworks/轮腿零件step/垂直梁x4.STEP

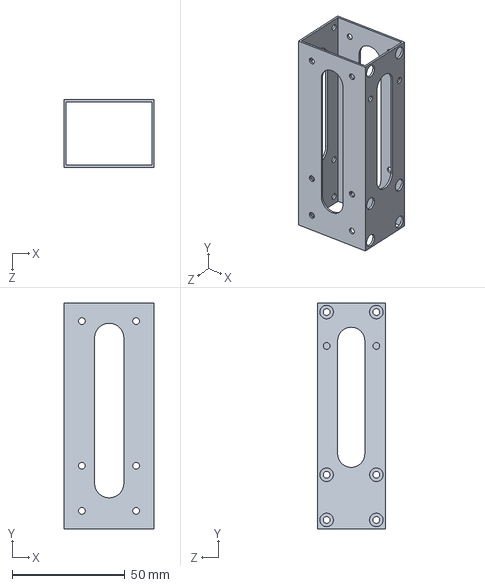
[picture p68: CAD file, 2024-12-23]
solidworks/轮腿零件step/垂直梁x4.STEP
40.0 x 100.0 x 30.0 mm
