Kevin16437/wheel_legged_robot/solidworks/轮腿零件step/关节电机固定板x2-碳板.STEP

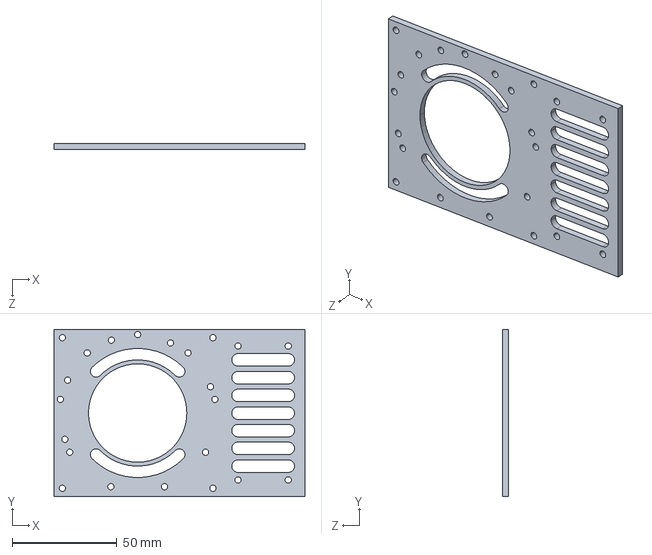
[picture p69: CAD file, 2024-12-23]
solidworks/轮腿零件step/关节电机固定板x2-碳板.STEP
120.0 x 80.0 x 3.00 mm
