Kevin16437/wheel_legged_robot/solidworks/轮腿装配图/法兰内16外22.SLDPRT

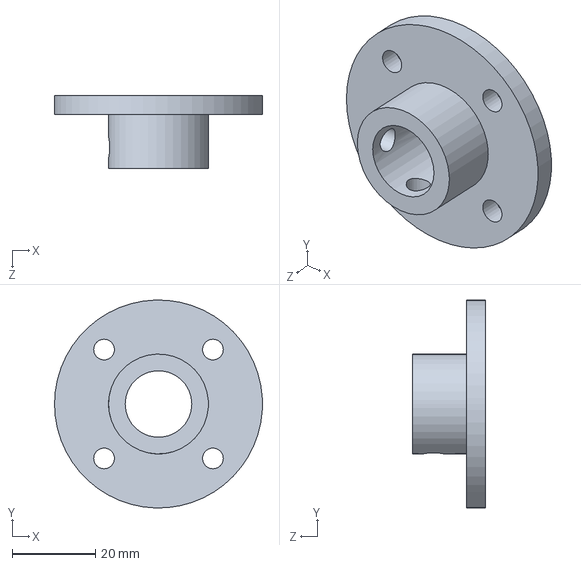
[picture p70: CAD file, 2024-12-23]
solidworks/轮腿装配图/法兰内16外22.SLDPRT
50.0 x 50.0 x 17.5 mm
