Kevin16437/wheel_legged_robot/software/WheelLegEmbedded/USER/Src/IMU_task.c

#include "IMU_task.h"

#define BMI088_BOARD_INSTALL_SPIN_MATRIX    \
    {1.0f, 0.0f, 0.0f},                     \
    {0.0f, 1.0f, 0.0f},                     \
    {0.0f, 0.0f, 1.0f}                      \

#define IST8310_BOARD_INSTALL_SPIN_MATRIX   \
    {1.0f, 0.0f, 0.0f},                     \
    {0.0f, 1.0f, 0.0f},                     \
    {0.0f, 0.0f, 1.0f}                      \
    
static void imu_cali_slove(float gyro[3], float accel[3], float mag[3], bmi088_real_data_t *bmi088, ist8310_real_data_t *ist8310);
static void imu_cmd_spi_dma(void);
void SPI1_DMA_init(uint32_t tx_buf, uint32_t rx_buf, uint16_t num);
void SPI1_DMA_enable(uint32_t tx_buf, uint32_t rx_buf, uint16_t ndtr);    

extern SPI_HandleTypeDef hspi1;
extern DMA_HandleTypeDef hdma_spi1_rx;
extern DMA_HandleTypeDef hdma_spi1_tx;

uint8_t gyro_dma_rx_buf[SPI_DMA_GYRO_LENGHT];
uint8_t gyro_dma_tx_buf[SPI_DMA_GYRO_LENGHT] = {0x82,0xFF,0xFF,0xFF,0xFF,0xFF,0xFF,0xFF};

uint8_t accel_dma_rx_buf[SPI_DMA_ACCEL_LENGHT];
uint8_t accel_dma_tx_buf[SPI_DMA_ACCEL_LENGHT] = {0x92,0xFF,0xFF,0xFF,0xFF,0xFF,0xFF,0xFF,0xFF};

uint8_t accel_temp_dma_rx_buf[SPI_DMA_ACCEL_TEMP_LENGHT];
uint8_t accel_temp_dma_tx_buf[SPI_DMA_ACCEL_TEMP_LENGHT] = {0xA2,0xFF,0xFF,0xFF};

volatile uint8_t gyro_update_flag = 0;
volatile uint8_t accel_update_flag = 0;
volatile uint8_t accel_temp_update_flag = 0;
volatile uint8_t mag_update_flag = 0;
volatile uint8_t imu_start_dma_flag = 0;

float gyro_scale_factor[3][3] = {BMI088_BOARD_INSTALL_SPIN_MATRIX};
float gyro_offset[3];
float gyro_cali_offset[3] = {0.0f, 0.0f, 0.0f};

float accel_scale_factor[3][3] = {BMI088_BOARD_INSTALL_SPIN_MATRIX};
float accel_offset[3];
float accel_cali_offset[3] = {0.0f, 0.0f, 0.0f};

float mag_scale_factor[3][3] = {IST8310_BOARD_INSTALL_SPIN_MATRIX};
float mag_offset[3];
float mag_cali_offset[3] = {0.0f, 0.0f, 0.0f};

static const float timing_time = 0.001f;   //tast run time , unit s.任务运行的时间 单位 s

/* 加速度计低通滤波 */
static float accel_fliter_1[3] = {0.0f, 0.0f, 0.0f};
static float accel_fliter_2[3] = {0.0f, 0.0f, 0.0f};
static float accel_fliter_3[3] = {0.0f, 0.0f, 0.0f};
static const float fliter_num[3] = {1.929454039488895f, -0.93178349823448126f, 0.002329458745586203f};

/* 采样频率，截止频率 */
float sample_freq = 1.0f /timing_time, cutoff_freq = 0.01f;

static float INS_gyro[3] = {0.0f, 0.0f, 0.0f};
static float INS_accel[3] = {0.0f, 0.0f, 0.0f};
static float INS_mag[3] = {0.0f, 0.0f, 0.0f};
static float INS_quat[4] = {0.0f, 0.0f, 0.0f, 0.0f};
float INS_angle[3] = {0.0f, 0.0f, 0.0f};      //euler angle, unit rad.欧拉角 单位 rad

/* 陀螺仪任务句柄 */
TaskHandle_t IMU_task_handler;
#ifdef UP_DEBUG
    float pitch_offset = -0.0195f;
#else     
    float pitch_offset = 0.0f;
#endif

/* 陀螺仪任务 */
void IMU_task(void const * argument) {
    /* 陀螺仪初始化 */
    while(BMI088_init()) osDelay(10);
    /* 磁力计初始化 */
    while(ist8310_init()) osDelay(10);

    /* 读取陀螺仪和加速度计的数据 */
    BMI088_read(bmi088_real_data.gyro, bmi088_real_data.accel, &bmi088_real_data.temp);

    /* 对IMU数据进行校准处理 */
    imu_cali_slove(INS_gyro, INS_accel, INS_mag, &bmi088_real_data, &ist8310_real_data);

    /* 初始化四元数 */
    AHRS_init(INS_quat, INS_accel, INS_mag);
    
    /* 初始化加速度计滤波器 */
    accel_fliter_1[0] = accel_fliter_2[0] = accel_fliter_3[0] = INS_accel[0];
    accel_fliter_1[1] = accel_fliter_2[1] = accel_fliter_3[1] = INS_accel[1];
    accel_fliter_1[2] = accel_fliter_2[2] = accel_fliter_3[2] = INS_accel[2];
    
    AHRS_update(INS_quat, timing_time, INS_gyro, accel_fliter_3, INS_mag);
    get_angle(INS_quat, INS_angle + INS_YAW_ADDRESS_OFFSET, INS_angle + INS_PITCH_ADDRESS_OFFSET, INS_angle + INS_ROLL_ADDRESS_OFFSET);
    imuData.yawOffset = INS_angle[INS_YAW_ADDRESS_OFFSET];

    /* SPI1初始化配置 */
    hspi1.Init.BaudRatePrescaler = SPI_BAUDRATEPRESCALER_8;
    if (HAL_SPI_Init(&hspi1) != HAL_OK)
        Error_Handler();

    /* 初始化SPI1的DMA */
    SPI1_DMA_init((uint32_t)gyro_dma_tx_buf, (uint32_t)gyro_dma_rx_buf, SPI_DMA_GYRO_LENGHT);

    /* 启动IMU的DMA传输 */
    imu_start_dma_flag = 1;
    
    /* 上一次Yaw值 */
    float lastYaw = 0.0f;
    
    for(;;) {
        while (ulTaskNotifyTake(pdTRUE, portMAX_DELAY) != pdPASS);
        
        /* 处理陀螺仪数据更新 */
        if(gyro_update_flag & (1 << IMU_NOTIFY_SHFITS))
        {
            gyro_update_flag &= ~(1 << IMU_NOTIFY_SHFITS);
            BMI088_gyro_read_over(gyro_dma_rx_buf + BMI088_GYRO_RX_BUF_DATA_OFFSET, bmi088_real_data.gyro);
        }

        /* 处理加速度计数据更新 */
        if(accel_update_flag & (1 << IMU_UPDATE_SHFITS))
        {
            accel_update_flag &= ~(1 << IMU_UPDATE_SHFITS);
            BMI088_accel_read_over(accel_dma_rx_buf + BMI088_ACCEL_RX_BUF_DATA_OFFSET, bmi088_real_data.accel, &bmi088_real_data.time);
        }

        /* 处理温度数据更新 */
        if(accel_temp_update_flag & (1 << IMU_UPDATE_SHFITS))
        {
            accel_temp_update_flag &= ~(1 << IMU_UPDATE_SHFITS);
            BMI088_temperature_read_over(accel_temp_dma_rx_buf + BMI088_ACCEL_RX_BUF_DATA_OFFSET, &bmi088_real_data.temp);
            /* 温控PID */
            PID_Control(&imuTempPID, bmi088_real_data.temp, 30.0f);
            /* 设置加热PWM占空比 */
            TIM10->CCR1 = (uint32_t)(imuTempPID.pid_out > 0.0f ? imuTempPID.pid_out : 0);
        }

        /* 对IMU数据进行校准处理 */
        imu_cali_slove(INS_gyro, INS_accel, INS_mag, &bmi088_real_data, &ist8310_real_data);

        //加速度计低通滤波
        accel_fliter_1[0] = accel_fliter_2[0];
        accel_fliter_2[0] = accel_fliter_3[0];
        accel_fliter_3[0] = accel_fliter_2[0] * fliter_num[0] + accel_fliter_1[0] * fliter_num[1] + INS_accel[0] * fliter_num[2];

        accel_fliter_1[1] = accel_fliter_2[1];
        accel_fliter_2[1] = accel_fliter_3[1];
        accel_fliter_3[1] = accel_fliter_2[1] * fliter_num[0] + accel_fliter_1[1] * fliter_num[1] + INS_accel[1] * fliter_num[2];

        accel_fliter_1[2] = accel_fliter_2[2];
        accel_fliter_2[2] = accel_fliter_3[2];
        accel_fliter_3[2] = accel_fliter_2[2] * fliter_num[0] + accel_fliter_1[2] * fliter_num[1] + INS_accel[2] * fliter_num[2];

        /* 更新四元数 */
        AHRS_update(INS_quat, timing_time, INS_gyro, accel_fliter_3, INS_mag);
        /* 获取欧拉角 */
        get_angle(INS_quat, INS_angle + INS_YAW_ADDRESS_OFFSET, INS_angle + INS_PITCH_ADDRESS_OFFSET, INS_angle + INS_ROLL_ADDRESS_OFFSET);
        
        /* yaw轴记圈 */
        float yaw = INS_angle[INS_YAW_ADDRESS_OFFSET];
        float diff = yaw - lastYaw;
        if (diff > PI) imuData.yawRound--;
        else if (diff < -PI) imuData.yawRound++;
        lastYaw = yaw;
        float yawLoopy = yaw + imuData.yawRound * 2.0f * PI - imuData.yawOffset;
        
        float *yawFilter, *rollFilter, *pitchFilter;
        yawFilter = KalmanII_Filter(&yawKalmanIIFilter, yawLoopy, INS_gyro[2]);
        rollFilter = KalmanII_Filter(&rollKalmanIIFilter, INS_angle[INS_ROLL_ADDRESS_OFFSET], INS_gyro[0]);
        pitchFilter = KalmanII_Filter(&pitchKalmanIIFilter, INS_angle[INS_PITCH_ADDRESS_OFFSET], INS_gyro[1]);
        
        /* 陀螺仪欧拉角解算数据获取 */  
        imuData.yaw = yawFilter[0];
        imuData.pitch = pitchFilter[0] - pitch_offset;
        imuData.roll = rollFilter[0];
        
        /* 陀螺仪角速度解算数据获取 */
        imuData.yawSpd = yawFilter[1];
        imuData.pitchSpd = pitchFilter[1];
        imuData.rollSpd = rollFilter[1];
        
        /* 陀螺仪z轴加速度解算数据获取 */
        imuData.zAccel = INS_accel[2];
    }
}

   /**
  * @brief          旋转陀螺仪,加速度计和磁力计,并计算零漂,因为设备有不同安装方式
  * @param[out]     gyro: 加上零漂和旋转
  * @param[out]     accel: 加上零漂和旋转
  * @param[out]     mag: 加上零漂和旋转
  * @param[in]      bmi088: 陀螺仪和加速度计数据
  * @param[in]      ist8310: 磁力计数据
  * @retval         none
  */
static void imu_cali_slove(float gyro[3], float accel[3], float mag[3], bmi088_real_data_t *bmi088, ist8310_real_data_t *ist8310)
{
    for (uint8_t i = 0; i < 3; i++)
    {
        gyro[i] = bmi088->gyro[0] * gyro_scale_factor[i][0] + bmi088->gyro[1] * gyro_scale_factor[i][1] + bmi088->gyro[2] * gyro_scale_factor[i][2] + gyro_offset[i];
        accel[i] = bmi088->accel[0] * accel_scale_factor[i][0] + bmi088->accel[1] * accel_scale_factor[i][1] + bmi088->accel[2] * accel_scale_factor[i][2] + accel_offset[i];
        mag[i] = ist8310->mag[0] * mag_scale_factor[i][0] + ist8310->mag[1] * mag_scale_factor[i][1] + ist8310->mag[2] * mag_scale_factor[i][2] + mag_offset[i];
    }
}

/**
  * @brief          calculate gyro zero drift
  * @param[out]     gyro_offset:zero drift
  * @param[in]      gyro:gyro data
  * @param[out]     offset_time_count: +1 auto
  * @retval         none
  */
/**
  * @brief          计算陀螺仪零漂
  * @param[out]     gyro_offset:计算零漂
  * @param[in]      gyro:角速度数据
  * @param[out]     offset_time_count: 自动加1
  * @retval         none
  */
void gyro_offset_calc(float gyro_offset[3], float gyro[3], uint16_t *offset_time_count)
{
    if (gyro_offset == NULL || gyro == NULL || offset_time_count == NULL)
    {
        return;
    }

        gyro_offset[0] = gyro_offset[0] - 0.0003f * gyro[0];
        gyro_offset[1] = gyro_offset[1] - 0.0003f * gyro[1];
        gyro_offset[2] = gyro_offset[2] - 0.0003f * gyro[2];
        (*offset_time_count)++;
}

/**
  * @brief          calculate gyro zero drift
  * @param[out]     cali_scale:scale, default 1.0
  * @param[out]     cali_offset:zero drift, collect the gyro ouput when in still
  * @param[out]     time_count: time, when call gyro_offset_calc 
  * @retval         none
  */
/**
  * @brief          校准陀螺仪
  * @param[out]     陀螺仪的比例因子，1.0f为默认值，不修改
  * @param[out]     陀螺仪的零漂，采集陀螺仪的静止的输出作为offset
  * @param[out]     陀螺仪的时刻，每次在gyro_offset调用会加1,
  * @retval         none
  */
void INS_cali_gyro(float cali_scale[3], float cali_offset[3], uint16_t *time_count)
{
        if( *time_count == 0)
        {
            gyro_offset[0] = gyro_cali_offset[0];
            gyro_offset[1] = gyro_cali_offset[1];
            gyro_offset[2] = gyro_cali_offset[2];
        }
        gyro_offset_calc(gyro_offset, INS_gyro, time_count);

        cali_offset[0] = gyro_offset[0];
        cali_offset[1] = gyro_offset[1];
        cali_offset[2] = gyro_offset[2];
        cali_scale[0] = 1.0f;
        cali_scale[1] = 1.0f;
        cali_scale[2] = 1.0f;

}

/**
  * @brief          get gyro zero drift from flash
  * @param[in]      cali_scale:scale, default 1.0
  * @param[in]      cali_offset:zero drift, 
  * @retval         none
  */
/**
  * @brief          校准陀螺仪设置，将从flash或者其他地方传入校准值
  * @param[in]      陀螺仪的比例因子，1.0f为默认值，不修改
  * @param[in]      陀螺仪的零漂
  * @retval         none
  */
void INS_set_cali_gyro(float cali_scale[3], float cali_offset[3])
{
    gyro_cali_offset[0] = cali_offset[0];
    gyro_cali_offset[1] = cali_offset[1];
    gyro_cali_offset[2] = cali_offset[2];
    gyro_offset[0] = gyro_cali_offset[0];
    gyro_offset[1] = gyro_cali_offset[1];
    gyro_offset[2] = gyro_cali_offset[2];
}

/**
  * @brief          get the quat
  * @param[in]      none
  * @retval         the point of INS_quat
  */
/**
  * @brief          获取四元数
  * @param[in]      none
  * @retval         INS_quat的指针
  */
const float *get_INS_quat_point(void)
{
    return INS_quat;
}
/**
  * @brief          get the euler angle, 0:yaw, 1:pitch, 2:roll unit rad
  * @param[in]      none
  * @retval         the point of INS_angle
  */
/**
  * @brief          获取欧拉角, 0:yaw, 1:pitch, 2:roll 单位 rad
  * @param[in]      none
  * @retval         INS_angle的指针
  */
const float *get_INS_angle_point(void)
{
    return INS_angle;
}

/**
  * @brief          get the rotation speed, 0:x-axis, 1:y-axis, 2:roll-axis,unit rad/s
  * @param[in]      none
  * @retval         the point of INS_gyro
  */
/**
  * @brief          获取角速度,0:x轴, 1:y轴, 2:roll轴 单位 rad/s
  * @param[in]      none
  * @retval         INS_gyro的指针
  */
extern const float *get_gyro_data_point(void)
{
    return INS_gyro;
}
/**
  * @brief          get aceel, 0:x-axis, 1:y-axis, 2:roll-axis unit m/s2
  * @param[in]      none
  * @retval         the point of INS_accel
  */
/**
  * @brief          获取加速度,0:x轴, 1:y轴, 2:roll轴 单位 m/s2
  * @param[in]      none
  * @retval         INS_accel的指针
  */
extern const float *get_accel_data_point(void)
{
    return INS_accel;
}
/**
  * @brief          get mag, 0:x-axis, 1:y-axis, 2:roll-axis unit ut
  * @param[in]      none
  * @retval         the point of INS_mag
  */
/**
  * @brief          获取加速度,0:x轴, 1:y轴, 2:roll轴 单位 ut
  * @param[in]      none
  * @retval         INS_mag的指针
  */
extern const float *get_mag_data_point(void)
{
    return INS_mag;
}

/**
  * @brief          open the SPI DMA accord to the value of imu_update_flag
  * @param[in]      none
  * @retval         none
  */
/**
  * @brief          根据imu_update_flag的值开启SPI DMA
  * @param[in]      temp:bmi088的温度
  * @retval         none
  */
static void imu_cmd_spi_dma(void)
{
    UBaseType_t uxSavedInterruptStatus;
    uxSavedInterruptStatus = taskENTER_CRITICAL_FROM_ISR();

    //开启陀螺仪的DMA传输
    if( (gyro_update_flag & (1 << IMU_DR_SHFITS) ) && !(hspi1.hdmatx->Instance->CR & DMA_SxCR_EN) && !(hspi1.hdmarx->Instance->CR & DMA_SxCR_EN)
    && !(accel_update_flag & (1 << IMU_SPI_SHFITS)) && !(accel_temp_update_flag & (1 << IMU_SPI_SHFITS)))
    {
        gyro_update_flag &= ~(1 << IMU_DR_SHFITS);
        gyro_update_flag |= (1 << IMU_SPI_SHFITS);

        HAL_GPIO_WritePin(CS1_GYRO_GPIO_Port, CS1_GYRO_Pin, GPIO_PIN_RESET);
        SPI1_DMA_enable((uint32_t)gyro_dma_tx_buf, (uint32_t)gyro_dma_rx_buf, SPI_DMA_GYRO_LENGHT);
        taskEXIT_CRITICAL_FROM_ISR(uxSavedInterruptStatus);
        return;
    }
    //开启加速度计的DMA传输
    if((accel_update_flag & (1 << IMU_DR_SHFITS)) && !(hspi1.hdmatx->Instance->CR & DMA_SxCR_EN) && !(hspi1.hdmarx->Instance->CR & DMA_SxCR_EN)
    && !(gyro_update_flag & (1 << IMU_SPI_SHFITS)) && !(accel_temp_update_flag & (1 << IMU_SPI_SHFITS)))
    {
        accel_update_flag &= ~(1 << IMU_DR_SHFITS);
        accel_update_flag |= (1 << IMU_SPI_SHFITS);

        HAL_GPIO_WritePin(CS1_ACCEL_GPIO_Port, CS1_ACCEL_Pin, GPIO_PIN_RESET);
        SPI1_DMA_enable((uint32_t)accel_dma_tx_buf, (uint32_t)accel_dma_rx_buf, SPI_DMA_ACCEL_LENGHT);
        taskEXIT_CRITICAL_FROM_ISR(uxSavedInterruptStatus);
        return;
    }
    
    if((accel_temp_update_flag & (1 << IMU_DR_SHFITS)) && !(hspi1.hdmatx->Instance->CR & DMA_SxCR_EN) && !(hspi1.hdmarx->Instance->CR & DMA_SxCR_EN)
    && !(gyro_update_flag & (1 << IMU_SPI_SHFITS)) && !(accel_update_flag & (1 << IMU_SPI_SHFITS)))
    {
        accel_temp_update_flag &= ~(1 << IMU_DR_SHFITS);
        accel_temp_update_flag |= (1 << IMU_SPI_SHFITS);

        HAL_GPIO_WritePin(CS1_ACCEL_GPIO_Port, CS1_ACCEL_Pin, GPIO_PIN_RESET);
        SPI1_DMA_enable((uint32_t)accel_temp_dma_tx_buf, (uint32_t)accel_temp_dma_rx_buf, SPI_DMA_ACCEL_TEMP_LENGHT);
        taskEXIT_CRITICAL_FROM_ISR(uxSavedInterruptStatus);
        return;
    }
    taskEXIT_CRITICAL_FROM_ISR(uxSavedInterruptStatus);
}

void SPI1_DMA_init(uint32_t tx_buf, uint32_t rx_buf, uint16_t num)
{
    SET_BIT(hspi1.Instance->CR2, SPI_CR2_TXDMAEN);
    SET_BIT(hspi1.Instance->CR2, SPI_CR2_RXDMAEN);

    __HAL_SPI_ENABLE(&hspi1);


    //disable DMA
    //失效DMA
    __HAL_DMA_DISABLE(&hdma_spi1_rx);
    
    while(hdma_spi1_rx.Instance->CR & DMA_SxCR_EN)
    {
        __HAL_DMA_DISABLE(&hdma_spi1_rx);
    }

    __HAL_DMA_CLEAR_FLAG(&hdma_spi1_rx, DMA_LISR_TCIF2);

    hdma_spi1_rx.Instance->PAR = (uint32_t) & (SPI1->DR);
    //memory buffer 1
    //内存缓冲区1
    hdma_spi1_rx.Instance->M0AR = (uint32_t)(rx_buf);
    //data length
    //数据长度
    __HAL_DMA_SET_COUNTER(&hdma_spi1_rx, num);

    __HAL_DMA_ENABLE_IT(&hdma_spi1_rx, DMA_IT_TC);


    //disable DMA
    //失效DMA
    __HAL_DMA_DISABLE(&hdma_spi1_tx);
    
    while(hdma_spi1_tx.Instance->CR & DMA_SxCR_EN)
    {
        __HAL_DMA_DISABLE(&hdma_spi1_tx);
    }


    __HAL_DMA_CLEAR_FLAG(&hdma_spi1_tx, DMA_LISR_TCIF3);

    hdma_spi1_tx.Instance->PAR = (uint32_t) & (SPI1->DR);
    //memory buffer 1
    //内存缓冲区1
    hdma_spi1_tx.Instance->M0AR = (uint32_t)(tx_buf);
    //data length
    //数据长度
    __HAL_DMA_SET_COUNTER(&hdma_spi1_tx, num);


}

void SPI1_DMA_enable(uint32_t tx_buf, uint32_t rx_buf, uint16_t ndtr)
{
    __HAL_DMA_DISABLE(&hdma_spi1_rx);
    __HAL_DMA_DISABLE(&hdma_spi1_tx);


    while(hdma_spi1_rx.Instance->CR & DMA_SxCR_EN)
    {
        __HAL_DMA_DISABLE(&hdma_spi1_rx);
    }
    while(hdma_spi1_tx.Instance->CR & DMA_SxCR_EN)
    {
        __HAL_DMA_DISABLE(&hdma_spi1_tx);
    }

    __HAL_DMA_CLEAR_FLAG (hspi1.hdmarx, __HAL_DMA_GET_TC_FLAG_INDEX(hspi1.hdmarx));
    __HAL_DMA_CLEAR_FLAG (hspi1.hdmarx, __HAL_DMA_GET_HT_FLAG_INDEX(hspi1.hdmarx));
    __HAL_DMA_CLEAR_FLAG (hspi1.hdmarx, __HAL_DMA_GET_TE_FLAG_INDEX(hspi1.hdmarx));
    __HAL_DMA_CLEAR_FLAG (hspi1.hdmarx, __HAL_DMA_GET_DME_FLAG_INDEX(hspi1.hdmarx));
    __HAL_DMA_CLEAR_FLAG (hspi1.hdmarx, __HAL_DMA_GET_FE_FLAG_INDEX(hspi1.hdmarx));

    __HAL_DMA_CLEAR_FLAG (hspi1.hdmatx, __HAL_DMA_GET_TC_FLAG_INDEX(hspi1.hdmatx));
    __HAL_DMA_CLEAR_FLAG (hspi1.hdmatx, __HAL_DMA_GET_HT_FLAG_INDEX(hspi1.hdmatx));
    __HAL_DMA_CLEAR_FLAG (hspi1.hdmatx, __HAL_DMA_GET_TE_FLAG_INDEX(hspi1.hdmatx));
    __HAL_DMA_CLEAR_FLAG (hspi1.hdmatx, __HAL_DMA_GET_DME_FLAG_INDEX(hspi1.hdmatx));
    __HAL_DMA_CLEAR_FLAG (hspi1.hdmatx, __HAL_DMA_GET_FE_FLAG_INDEX(hspi1.hdmatx));


    hdma_spi1_rx.Instance->M0AR = rx_buf;
    hdma_spi1_tx.Instance->M0AR = tx_buf;

    __HAL_DMA_SET_COUNTER(&hdma_spi1_rx, ndtr);
    __HAL_DMA_SET_COUNTER(&hdma_spi1_tx, ndtr);

    __HAL_DMA_ENABLE(&hdma_spi1_rx);
    __HAL_DMA_ENABLE(&hdma_spi1_tx);
}

void HAL_GPIO_EXTI_Callback(uint16_t GPIO_Pin)
{
    if(GPIO_Pin == INT1_ACCEL_Pin)
    {
        accel_update_flag |= 1 << IMU_DR_SHFITS;
        accel_temp_update_flag |= 1 << IMU_DR_SHFITS;
        if(imu_start_dma_flag)
        {
            imu_cmd_spi_dma();
        }
    }
    else if(GPIO_Pin == INT1_GYRO_Pin)
    {
        gyro_update_flag |= 1 << IMU_DR_SHFITS;
        if(imu_start_dma_flag)
        {
            imu_cmd_spi_dma();
        }
    }
    else if(GPIO_Pin == DRDY_IST8310_Pin)
    {
        mag_update_flag |= 1 << IMU_DR_SHFITS;
        
        if(mag_update_flag &= 1 << IMU_DR_SHFITS)
        {
            mag_update_flag &= ~(1<< IMU_DR_SHFITS);
            mag_update_flag |= (1 << IMU_SPI_SHFITS);

            ist8310_read_mag(ist8310_real_data.mag);
        }
    }
    else if(GPIO_Pin == GPIO_PIN_0)
    {
        //wake up the task
        //唤醒任务
        if (xTaskGetSchedulerState() != taskSCHEDULER_NOT_STARTED)
        {
            static BaseType_t xHigherPriorityTaskWoken;
            vTaskNotifyGiveFromISR(IMU_task_handler, &xHigherPriorityTaskWoken);
            portYIELD_FROM_ISR(xHigherPriorityTaskWoken);
        }

    }
}

void DMA2_Stream2_IRQHandler(void)
{

    if(__HAL_DMA_GET_FLAG(hspi1.hdmarx, __HAL_DMA_GET_TC_FLAG_INDEX(hspi1.hdmarx)) != RESET)
    {
        __HAL_DMA_CLEAR_FLAG(hspi1.hdmarx, __HAL_DMA_GET_TC_FLAG_INDEX(hspi1.hdmarx));

        //gyro read over
        //陀螺仪读取完毕
        if(gyro_update_flag & (1 << IMU_SPI_SHFITS))
        {
            gyro_update_flag &= ~(1 << IMU_SPI_SHFITS);
            gyro_update_flag |= (1 << IMU_UPDATE_SHFITS);

            HAL_GPIO_WritePin(CS1_GYRO_GPIO_Port, CS1_GYRO_Pin, GPIO_PIN_SET);
            
        }

        //accel read over
        //加速度计读取完毕
        if(accel_update_flag & (1 << IMU_SPI_SHFITS))
        {
            accel_update_flag &= ~(1 << IMU_SPI_SHFITS);
            accel_update_flag |= (1 << IMU_UPDATE_SHFITS);

            HAL_GPIO_WritePin(CS1_ACCEL_GPIO_Port, CS1_ACCEL_Pin, GPIO_PIN_SET);
        }
        //temperature read over
        //温度读取完毕
        if(accel_temp_update_flag & (1 << IMU_SPI_SHFITS))
        {
            accel_temp_update_flag &= ~(1 << IMU_SPI_SHFITS);
            accel_temp_update_flag |= (1 << IMU_UPDATE_SHFITS);

            HAL_GPIO_WritePin(CS1_ACCEL_GPIO_Port, CS1_ACCEL_Pin, GPIO_PIN_SET);
        }
        
        imu_cmd_spi_dma();

        if(gyro_update_flag & (1 << IMU_UPDATE_SHFITS))
        {
            gyro_update_flag &= ~(1 << IMU_UPDATE_SHFITS);
            gyro_update_flag |= (1 << IMU_NOTIFY_SHFITS);
            __HAL_GPIO_EXTI_GENERATE_SWIT(GPIO_PIN_0);
        }
    }
}
