Kevin16437/wheel_legged_robot/software/WheelLegEmbedded/USER/Inc/IMU_task.h

#ifndef _IMU_TASK_H
#define _IMU_TASK_H

#include "start_init_task.h"

#define SPI_DMA_GYRO_LENGHT       8
#define SPI_DMA_ACCEL_LENGHT      9
#define SPI_DMA_ACCEL_TEMP_LENGHT 4

#define IMU_DR_SHFITS        0
#define IMU_SPI_SHFITS       1
#define IMU_UPDATE_SHFITS    2
#define IMU_NOTIFY_SHFITS    3

#define BMI088_GYRO_RX_BUF_DATA_OFFSET  1
#define BMI088_ACCEL_RX_BUF_DATA_OFFSET 2

//ist83100原始数据在缓冲区buf的位置
#define IST8310_RX_BUF_DATA_OFFSET 16

#define INS_YAW_ADDRESS_OFFSET    0
#define INS_PITCH_ADDRESS_OFFSET  1
#define INS_ROLL_ADDRESS_OFFSET   2

#define INS_GYRO_X_ADDRESS_OFFSET 0
#define INS_GYRO_Y_ADDRESS_OFFSET 1
#define INS_GYRO_Z_ADDRESS_OFFSET 2

#define INS_ACCEL_X_ADDRESS_OFFSET 0
#define INS_ACCEL_Y_ADDRESS_OFFSET 1
#define INS_ACCEL_Z_ADDRESS_OFFSET 2

#define INS_MAG_X_ADDRESS_OFFSET 0
#define INS_MAG_Y_ADDRESS_OFFSET 1
#define INS_MAG_Z_ADDRESS_OFFSET 2

// 低通滤波器结构体
typedef struct {
    float filtered_value;  // 滤波后的输出值
    float alpha;           // 滤波系数
} LowPassFilter;

extern SPI_HandleTypeDef hspi1;

extern TaskHandle_t IMU_task_handler;

void IMU_task(void const * argument);

#endif
